IoTReady/low-power-nrf52-weighing-scale/firmware/platform/weighing_scale_hx711.h

/**
 *  pca10040.h : PCA10040 board definitions
 *  Copyright (C) 2019  Appiko
 *
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
 *  You should have received a copy of the GNU General Public License
 *  along with this program.  If not, see <https://www.gnu.org/licenses/>.
 */

/**
 * @addtogroup group_platform
 * @{
 *
 * @defgroup board_pca10040 PCA10040 nRF52-DK
 * @brief The nRF52 Development Kit (DK) platform PCA10040
 * @{
 */

#ifndef PLATFORM_W_SCALE_HX711
#define PLATFORM_W_SCALE_HX711

/** @anchor general-gpio
 * @name General GPIO definitions
 * @{*/
#define GPIO_0          (17)
#define GPIO_1          (16)
#define GPIO_2          (15)
#define GPIO_3          (14)
/** The output level at which the LEDs shine */
#define LEDS_ACTIVE_STATE (0)
/** @} */

/** @anchor weighing_scale_button
 * @name Button Pins
 * @{*/
#define BUTTON_PIN      (7)
/** The input level when the button is pressed */
#define BUTTONS_ACTIVE_STATE (0)
/** The kind of internal resistors required for the button */
#define BUTTON_PULL     (HAL_GPIO_PULLUP)
/** @} */

/** @anchor weighing_scale_serial_interface
 * @name Serial port definitions for Weighing Scale HX711 board
 * @{*/
#define RX_PIN_NUMBER   (21)
#define TX_PIN_NUMBER   (20)
#define CTS_PIN_NUMBER  (7)
#define RTS_PIN_NUMBER  (5)
/** Bool to say if the hardware flow control is required */
#define HWFC            (false)
/** @} */

/** @anchor e_ink_paper_interface 
 * @name E-Ink Paper display Interface
 * @{*/
#define EINK_BUSY       (GPIO_0)
#define EINK_RST        (GPIO_1)
#define EINK_DC         (GPIO_2)
#define EINK_CS         (GPIO_3)
#define EINK_SCLK       (TX_PIN_NUMBER)
#define EINK_MOSI       (RX_PIN_NUMBER)
#define EINK_MISO       (31) //Unused
/** @} */

#if 0
#define EINK_BUSY       (25)
#define EINK_RST        (26)
#define EINK_DC         (27)
#define EINK_CS         (28)
#define EINK_SCLK       (29)
#define EINK_MOSI       (30)
#endif

/** @anchor hx711_interface 
 * @name HX711 Interface
 * @{*/
#define HX711_CLK       (13)
#define HX711_DATA      (12)
#define HX711_RATE      (11)
#define VLC_PIN         (4)
#define LDO_EN          (8)
#define BOOST_EN        (9)
/** @} */

/** @anchor batt_level 
 * @name Battery Level
 * @{*/
#define BT_LV           (5)
#define BT_LV_ANALOG    (ANALOG_PIN_5)
#define BT_LV_EN        (10)
/** @} */

///Bool define if the circuitry is present for the internal DC-DC of nRF52
#define DC_DC_CIRCUITRY     true

///Bool define if a NFC Antenna circuitry is present
#define NFC_CIRCUITRY       true

///Bool define if the 32 kHz crystal is present for the LFCLK
#define LFCLK_XTAL_PRESENT  true

///Bool define if a crystal is present for the HFCLK
#define HFCLK_XTAL_PRESENT  true

/** Low frequency clock source used when initializing the SoftDevice */
#define BOARD_LFCLKSRC_STRUCT  {.source        = NRF_CLOCK_LF_SRC_XTAL,            \
                                    .rc_ctiv       = 0,                                \
                                    .rc_temp_ctiv  = 0,                                \
                                    .accuracy = NRF_CLOCK_LF_ACCURACY_20_PPM}

#define BOARD_LFCLKSRC         LFCLK_SRC_Xtal

#endif /* PLATFORM_W_SCALE_HX711 */

/** @} */
/** @} */
