IoTReady/low-power-nrf52-weighing-scale/firmware/codebase/nrf_core/nrf52810_peripherals.h

/*

Copyright (c) 2010 - 2018, Nordic Semiconductor ASA All rights reserved.

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
1. Redistributions of source code must retain the above copyright notice, this
   list of conditions and the following disclaimer.

2. Redistributions in binary form must reproduce the above copyright
   notice, this list of conditions and the following disclaimer in the
   documentation and/or other materials provided with the distribution.

3. Neither the name of Nordic Semiconductor ASA nor the names of its
   contributors may be used to endorse or promote products derived from this
   software without specific prior written permission.

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
*/

#ifndef _NRF52810_PERIPHERALS_H
#define _NRF52810_PERIPHERALS_H


/* Power Peripheral */
#define POWER_PRESENT
#define POWER_COUNT 1

#define POWER_FEATURE_RAM_REGISTERS_PRESENT
#define POWER_FEATURE_RAM_REGISTERS_COUNT       3

/* Systick timer */
#define SYSTICK_PRESENT
#define SYSTICK_COUNT 1

/* Software Interrupts */
#define SWI_PRESENT
#define SWI_COUNT 6

/* GPIO */
#define GPIO_PRESENT
#define GPIO_COUNT 1

#define P0_PIN_NUM 32

/* MPU and BPROT */
#define BPROT_PRESENT

#define BPROT_REGIONS_SIZE 4096
#define BPROT_REGIONS_NUM 48

/* Radio */
#define RADIO_PRESENT
#define RADIO_COUNT 1

#define RADIO_EASYDMA_MAXCNT_SIZE 8

/* Accelerated Address Resolver */
#define AAR_PRESENT
#define AAR_COUNT 1

#define AAR_MAX_IRK_NUM 16

/* AES Electronic CodeBook mode encryption */
#define ECB_PRESENT
#define ECB_COUNT 1

/* AES CCM mode encryption */
#define CCM_PRESENT
#define CCM_COUNT 1

/* Peripheral to Peripheral Interconnect */
#define PPI_PRESENT
#define PPI_COUNT 1

#define PPI_CH_NUM 20
#define PPI_FIXED_CH_NUM 12
#define PPI_GROUP_NUM 6
#define PPI_FEATURE_FORKS_PRESENT

/* Event Generator Unit */
#define EGU_PRESENT
#define EGU_COUNT 2

#define EGU0_CH_NUM 16
#define EGU1_CH_NUM 16

/* Timer/Counter */
#define TIMER_PRESENT
#define TIMER_COUNT 3

#define TIMER0_MAX_SIZE 32
#define TIMER1_MAX_SIZE 32
#define TIMER2_MAX_SIZE 32

#define TIMER0_CC_NUM 4
#define TIMER1_CC_NUM 4
#define TIMER2_CC_NUM 4

/* Real Time Counter */
#define RTC_PRESENT
#define RTC_COUNT 2

#define RTC0_CC_NUM 3
#define RTC1_CC_NUM 4

/* RNG */
#define RNG_PRESENT
#define RNG_COUNT 1

/* Watchdog Timer */
#define WDT_PRESENT
#define WDT_COUNT 1

/* Temperature Sensor */
#define TEMP_PRESENT
#define TEMP_COUNT 1

/* Serial Peripheral Interface Master with DMA */
#define SPIM_PRESENT
#define SPIM_COUNT 1

#define SPIM0_MAX_DATARATE  8

#define SPIM0_FEATURE_HARDWARE_CSN_PRESENT  0

#define SPIM0_FEATURE_DCX_PRESENT  0

#define SPIM0_FEATURE_RXDELAY_PRESENT  0

#define SPIM0_EASYDMA_MAXCNT_SIZE 10

/* Serial Peripheral Interface Slave with DMA*/
#define SPIS_PRESENT
#define SPIS_COUNT 1

#define SPIS0_EASYDMA_MAXCNT_SIZE 10

/* Two Wire Interface Master with DMA */
#define TWIM_PRESENT
#define TWIM_COUNT 1

#define TWIM0_EASYDMA_MAXCNT_SIZE 10

/* Two Wire Interface Slave with DMA */
#define TWIS_PRESENT
#define TWIS_COUNT 1

#define TWIS0_EASYDMA_MAXCNT_SIZE 10

/* Universal Asynchronous Receiver-Transmitter with DMA */
#define UARTE_PRESENT
#define UARTE_COUNT 1

#define UARTE0_EASYDMA_MAXCNT_SIZE 10

/* Quadrature Decoder */
#define QDEC_PRESENT
#define QDEC_COUNT 1

/* Successive Approximation Analog to Digital Converter */
#define SAADC_PRESENT
#define SAADC_COUNT 1

#define SAADC_EASYDMA_MAXCNT_SIZE 15

#define SAADC_CH_NUM 8

/* GPIO Tasks and Events */
#define GPIOTE_PRESENT
#define GPIOTE_COUNT 1

#define GPIOTE_CH_NUM 8

#define GPIOTE_FEATURE_SET_PRESENT
#define GPIOTE_FEATURE_CLR_PRESENT

/* Comparator */
#define COMP_PRESENT
#define COMP_COUNT 1

/* Pulse Width Modulator */
#define PWM_PRESENT
#define PWM_COUNT 1

#define PWM0_CH_NUM 4

#define PWM0_EASYDMA_MAXCNT_SIZE 15

/* Pulse Density Modulator */
#define PDM_PRESENT
#define PDM_COUNT 1

#define PDM_EASYDMA_MAXCNT_SIZE 15


#endif      // _NRF52810_PERIPHERALS_H
