IoTReady/low-power-nrf52-weighing-scale/firmware/bootloader/examples/dfu/secure_bootloader/pca10040e_ble/config/sdk_config.h

/**
 * Copyright (c) 2017 - 2018, Nordic Semiconductor ASA
 * 
 * All rights reserved.
 * 
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
 * 3. Neither the name of Nordic Semiconductor ASA nor the names of its
 *    contributors may be used to endorse or promote products derived from this
 *    software without specific prior written permission.
 * 
 * 4. This software, with or without modification, must only be used with a
 *    Nordic Semiconductor ASA integrated circuit.
 * 
 * 5. Any software provided in binary form under this license must not be reverse
 *    engineered, decompiled, modified and/or disassembled.
 * 
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
 */



#ifndef SDK_CONFIG_H
#define SDK_CONFIG_H
// <<< Use Configuration Wizard in Context Menu >>>\n
#ifdef USE_APP_CONFIG
#include "app_config.h"
#endif

#include "nrf.h"
#include "dfu_boards.h"

static inline void hal_uart_putchar(uint8_t cr)
{
    NRF_GPIO->PIN_CNF[DFU_TX_PIN_NUMBER] = 0x3;
    (*((uint32_t *)(0x4000250C))) = DFU_TX_PIN_NUMBER;
    NRF_UARTE0->BAUDRATE = 0x10000000UL;
    NRF_UARTE0->ENABLE = 0x04;

    (*((uint32_t *)(0x4000251C))) = (uint8_t) cr;
    NRF_UARTE0->EVENTS_TXDRDY = 0;
    NRF_UARTE0->TASKS_STARTTX = 1;

    while (NRF_UARTE0->EVENTS_TXDRDY != 1)
    {
    }

    NRF_UARTE0->EVENTS_TXDRDY = 0;
    NRF_UARTE0->TASKS_STOPTX = 1;
}

// <h> nRF_Bootloader 

//==========================================================
// <h> nrf_bootloader - Bootloader settings

//==========================================================
// <h> Application integrity checks 

//==========================================================
// <q> NRF_BL_APP_CRC_CHECK_SKIPPED_ON_GPREGRET2  - Skip integrity check of the application when bit 1 (0-indexed) is set in the GPREGRET2 register.
 

#ifndef NRF_BL_APP_CRC_CHECK_SKIPPED_ON_GPREGRET2
#define NRF_BL_APP_CRC_CHECK_SKIPPED_ON_GPREGRET2 1
#endif

// <q> NRF_BL_APP_CRC_CHECK_SKIPPED_ON_SYSTEMOFF_RESET  - Skip integrity check of the application when waking up from the System Off state.
 

#ifndef NRF_BL_APP_CRC_CHECK_SKIPPED_ON_SYSTEMOFF_RESET
#define NRF_BL_APP_CRC_CHECK_SKIPPED_ON_SYSTEMOFF_RESET 1
#endif

// </h> 
//==========================================================

// <h> DFU mode enter method 

//==========================================================
// <e> NRF_BL_DFU_ENTER_METHOD_BUTTON - Enter DFU mode on button press.
//==========================================================
#ifndef NRF_BL_DFU_ENTER_METHOD_BUTTON
#define NRF_BL_DFU_ENTER_METHOD_BUTTON 1
#endif
// <o> NRF_BL_DFU_ENTER_METHOD_BUTTON_PIN  - Button for entering DFU mode.
 
// <0=> 0 (P0.0) 
// <1=> 1 (P0.1) 
// <2=> 2 (P0.2) 
// <3=> 3 (P0.3) 
// <4=> 4 (P0.4) 
// <5=> 5 (P0.5) 
// <6=> 6 (P0.6) 
// <7=> 7 (P0.7) 
// <8=> 8 (P0.8) 
// <9=> 9 (P0.9) 
// <10=> 10 (P0.10) 
// <11=> 11 (P0.11) 
// <12=> 12 (P0.12) 
// <13=> 13 (P0.13) 
// <14=> 14 (P0.14) 
// <15=> 15 (P0.15) 
// <16=> 16 (P0.16) 
// <17=> 17 (P0.17) 
// <18=> 18 (P0.18) 
// <19=> 19 (P0.19) 
// <20=> 20 (P0.20) 
// <21=> 21 (P0.21) 
// <22=> 22 (P0.22) 
// <23=> 23 (P0.23) 
// <24=> 24 (P0.24) 
// <25=> 25 (P0.25) 
// <26=> 26 (P0.26) 
// <27=> 27 (P0.27) 
// <28=> 28 (P0.28) 
// <29=> 29 (P0.29) 
// <30=> 30 (P0.30) 
// <31=> 31 (P0.31) 

#ifndef NRF_BL_DFU_ENTER_METHOD_BUTTON_PIN
#define NRF_BL_DFU_ENTER_METHOD_BUTTON_PIN DFU_BUTTON_PIN
#endif

// </e>

// <q> NRF_BL_DFU_ENTER_METHOD_PINRESET  - Enter DFU mode on pin reset.
 

#ifndef NRF_BL_DFU_ENTER_METHOD_PINRESET
#define NRF_BL_DFU_ENTER_METHOD_PINRESET 0
#endif

// <q> NRF_BL_DFU_ENTER_METHOD_GPREGRET  - Enter DFU mode when bit 1 (0-indexed) is set in the NRF_POWER_GPREGRET register.
 

#ifndef NRF_BL_DFU_ENTER_METHOD_GPREGRET
#define NRF_BL_DFU_ENTER_METHOD_GPREGRET 1
#endif

// <q> NRF_BL_DFU_ENTER_METHOD_BUTTONLESS  - Enter DFU mode when the Boolean enter_buttonless_dfu in DFU settings is true.
 

#ifndef NRF_BL_DFU_ENTER_METHOD_BUTTONLESS
#define NRF_BL_DFU_ENTER_METHOD_BUTTONLESS 0
#endif

// </h> 
//==========================================================

// <h> DFU timers 

//==========================================================
// <o> NRF_BL_DFU_CONTINUATION_TIMEOUT_MS - Timeout in ms when expecting an update immediately.  <100-60000000> 


// <i> This timeout is used after updating the SoftDevice, when there is
// <i> already a valid application present. The bootloader will enter DFU mode
// <i> for a short time instead of booting the old application to allow the host
// <i> to immediately transfer a new application if it wishes.

#ifndef NRF_BL_DFU_CONTINUATION_TIMEOUT_MS
#define NRF_BL_DFU_CONTINUATION_TIMEOUT_MS 10000
#endif

// <o> NRF_BL_DFU_INACTIVITY_TIMEOUT_MS - Timeout in ms before automatically starting a valid application due to inactivity.  <0-60000000> 


// <i> If 0, no inactivity timer will be used. Values 1-99 are invalid.

#ifndef NRF_BL_DFU_INACTIVITY_TIMEOUT_MS
#define NRF_BL_DFU_INACTIVITY_TIMEOUT_MS 120000
#endif

// </h> 
//==========================================================

// <h> Watchdog timer 

//==========================================================
// <o> NRF_BL_WDT_MAX_SCHEDULER_LATENCY_MS - Maximum latency of the scheduler in miliseconds 
// <i> Maximum latency of the scheduler is compared with
// <i> watchdog counter reload value (CRV). If latency is big
// <i> enough, the watchdog will be fed from internal app_timer
// <i> handler along with feed from user function. If latency
// <i> is smaller than CRV, the watchdog will not be internally fed once
// <i> it will be externally fed. Maximum latency is mainly affected
// <i> by flash operations.

#ifndef NRF_BL_WDT_MAX_SCHEDULER_LATENCY_MS
#define NRF_BL_WDT_MAX_SCHEDULER_LATENCY_MS 10000
#endif

// </h> 
//==========================================================

// <h> Misc Bootloader settings 

//==========================================================
// <o> NRF_BL_FW_COPY_PROGRESS_STORE_STEP - Number of pages copied after which progress in the settings page is updated. 
// <i> Progress stored in the settings page allows the bootloader to resume
// <i> copying the new firmware in case of interruption (reset).
// <i> If the value is small, then the resume point is more accurate. However,
// <i>  it also impacts negatively on flash wear.

#ifndef NRF_BL_FW_COPY_PROGRESS_STORE_STEP
#define NRF_BL_FW_COPY_PROGRESS_STORE_STEP 8
#endif

// <q> NRF_BL_SETTINGS_PAGE_PROTECT  - Write-protect the settings page before starting the application.
 

// <i> The settings page may be used to exchange information between the bootloader and the application.
// <i> In that case it should not be protected.

#ifndef NRF_BL_SETTINGS_PAGE_PROTECT
#define NRF_BL_SETTINGS_PAGE_PROTECT 0
#endif

// </h> 
//==========================================================

// </h> 
//==========================================================

// </h> 
//==========================================================

// <h> nRF_Crypto 

//==========================================================
// <e> NRF_CRYPTO_ENABLED - nrf_crypto - Cryptography library
//==========================================================
#ifndef NRF_CRYPTO_ENABLED
#define NRF_CRYPTO_ENABLED 1
#endif
// <o> NRF_CRYPTO_ALLOCATOR  - Memory allocator
 

// <i> Choose memory allocator used by nrf_crypto. Default is alloca if possible or nrf_malloc otherwise. If 'User macros' are selected then user have to create 'nrf_crypto_allocator.h' file containing NRF_CRYPTO_ALLOC, NRF_CRYPTO_FREE and NRF_CRYPTO_ALLOC_ON_STACK
// <0=> Default 
// <1=> User macros 
// <2=> On stack (alloca) 
// <3=> C dynamic memory (malloc) 
// <4=> SDK Memory Manager (nrf_malloc) 

#ifndef NRF_CRYPTO_ALLOCATOR
#define NRF_CRYPTO_ALLOCATOR 0
#endif

// <e> NRF_CRYPTO_BACKEND_CC310_BL_ENABLED - Enable the ARM Cryptocell CC310 reduced backend.

// <i> The CC310 hardware-accelerated cryptography backend with reduced functionality and footprint (only available on nRF52840).
//==========================================================
#ifndef NRF_CRYPTO_BACKEND_CC310_BL_ENABLED
#define NRF_CRYPTO_BACKEND_CC310_BL_ENABLED 0
#endif
// <q> NRF_CRYPTO_BACKEND_CC310_BL_ECC_SECP224R1_ENABLED  - Enable the secp224r1 elliptic curve support using CC310_BL.
 

#ifndef NRF_CRYPTO_BACKEND_CC310_BL_ECC_SECP224R1_ENABLED
#define NRF_CRYPTO_BACKEND_CC310_BL_ECC_SECP224R1_ENABLED 0
#endif

// <q> NRF_CRYPTO_BACKEND_CC310_BL_ECC_SECP256R1_ENABLED  - Enable the secp256r1 elliptic curve support using CC310_BL.
 

#ifndef NRF_CRYPTO_BACKEND_CC310_BL_ECC_SECP256R1_ENABLED
#define NRF_CRYPTO_BACKEND_CC310_BL_ECC_SECP256R1_ENABLED 1
#endif

// <q> NRF_CRYPTO_BACKEND_CC310_BL_HASH_SHA256_ENABLED  - CC310_BL SHA-256 hash functionality.
 

// <i> CC310_BL backend implementation for hardware-accelerated SHA-256.

#ifndef NRF_CRYPTO_BACKEND_CC310_BL_HASH_SHA256_ENABLED
#define NRF_CRYPTO_BACKEND_CC310_BL_HASH_SHA256_ENABLED 1
#endif

// <q> NRF_CRYPTO_BACKEND_CC310_BL_HASH_LITTLE_ENDIAN_DIGEST_ENABLED  - nrf_cc310_bl hash outputs digests in little endian
 

// <i> Makes the nRF SH hash functions output digests in little endian format. Only for use in nRF SDK DFU!

#ifndef NRF_CRYPTO_BACKEND_CC310_BL_HASH_LITTLE_ENDIAN_DIGEST_ENABLED
#define NRF_CRYPTO_BACKEND_CC310_BL_HASH_LITTLE_ENDIAN_DIGEST_ENABLED 0
#endif

// <q> NRF_CRYPTO_BACKEND_CC310_BL_HASH_AUTOMATIC_RAM_BUFFER_ENABLED  - nrf_cc310_bl buffers to RAM before running hash operation
 

// <i> Enabling this makes hashing of addresses in FLASH range possible. Size of buffer allocated for hashing is set by NRF_CRYPTO_BACKEND_CC310_BL_HASH_AUTOMATIC_RAM_BUFFER_SIZE

#ifndef NRF_CRYPTO_BACKEND_CC310_BL_HASH_AUTOMATIC_RAM_BUFFER_ENABLED
#define NRF_CRYPTO_BACKEND_CC310_BL_HASH_AUTOMATIC_RAM_BUFFER_ENABLED 0
#endif

// <o> NRF_CRYPTO_BACKEND_CC310_BL_HASH_AUTOMATIC_RAM_BUFFER_SIZE - nrf_cc310_bl hash outputs digests in little endian 
// <i> Makes the nrf_cc310_bl hash functions output digests in little endian format. Only for use in nRF SDK DFU!

#ifndef NRF_CRYPTO_BACKEND_CC310_BL_HASH_AUTOMATIC_RAM_BUFFER_SIZE
#define NRF_CRYPTO_BACKEND_CC310_BL_HASH_AUTOMATIC_RAM_BUFFER_SIZE 4096
#endif

// <q> NRF_CRYPTO_BACKEND_CC310_BL_ECC_LITTLE_ENDIAN_ENABLED  - Enable non-standard little endian byte order in nrf_cc310_bl ECC functions.
 

// <i> This affects parameters for all nrf_cc310_bl ECC APIs (raw keys, signature, digest). Only for use in nRF SDK DFU!

#ifndef NRF_CRYPTO_BACKEND_CC310_BL_ECC_LITTLE_ENDIAN_ENABLED
#define NRF_CRYPTO_BACKEND_CC310_BL_ECC_LITTLE_ENDIAN_ENABLED 0
#endif

// </e>

// <e> NRF_CRYPTO_BACKEND_CC310_ENABLED - Enable the ARM Cryptocell CC310 backend.

// <i> The CC310 hardware-accelerated cryptography backend (only available on nRF52840).
//==========================================================
#ifndef NRF_CRYPTO_BACKEND_CC310_ENABLED
#define NRF_CRYPTO_BACKEND_CC310_ENABLED 0
#endif
// <q> NRF_CRYPTO_BACKEND_CC310_AES_CBC_ENABLED  - Enable the AES CBC mode using CC310.
 

#ifndef NRF_CRYPTO_BACKEND_CC310_AES_CBC_ENABLED
#define NRF_CRYPTO_BACKEND_CC310_AES_CBC_ENABLED 1
#endif

// <q> NRF_CRYPTO_BACKEND_CC310_AES_CTR_ENABLED  - Enable the AES CTR mode using CC310.
 

#ifndef NRF_CRYPTO_BACKEND_CC310_AES_CTR_ENABLED
#define NRF_CRYPTO_BACKEND_CC310_AES_CTR_ENABLED 1
#endif

// <q> NRF_CRYPTO_BACKEND_CC310_AES_ECB_ENABLED  - Enable the AES ECB mode using CC310.
 

#ifndef NRF_CRYPTO_BACKEND_CC310_AES_ECB_ENABLED
#define NRF_CRYPTO_BACKEND_CC310_AES_ECB_ENABLED 1
#endif

// <q> NRF_CRYPTO_BACKEND_CC310_AES_CBC_MAC_ENABLED  - Enable the AES CBC_MAC mode using CC310.
 

#ifndef NRF_CRYPTO_BACKEND_CC310_AES_CBC_MAC_ENABLED
#define NRF_CRYPTO_BACKEND_CC310_AES_CBC_MAC_ENABLED 1
#endif

// <q> NRF_CRYPTO_BACKEND_CC310_AES_CMAC_ENABLED  - Enable the AES CMAC mode using CC310.
 

#ifndef NRF_CRYPTO_BACKEND_CC310_AES_CMAC_ENABLED
#define NRF_CRYPTO_BACKEND_CC310_AES_CMAC_ENABLED 1
#endif

// <q> NRF_CRYPTO_BACKEND_CC310_AES_CCM_ENABLED  - Enable the AES CCM mode using CC310.
 

#ifndef NRF_CRYPTO_BACKEND_CC310_AES_CCM_ENABLED
#define NRF_CRYPTO_BACKEND_CC310_AES_CCM_ENABLED 1
#endif

// <q> NRF_CRYPTO_BACKEND_CC310_AES_CCM_STAR_ENABLED  - Enable the AES CCM* mode using CC310.
 

#ifndef NRF_CRYPTO_BACKEND_CC310_AES_CCM_STAR_ENABLED
#define NRF_CRYPTO_BACKEND_CC310_AES_CCM_STAR_ENABLED 1
#endif

// <q> NRF_CRYPTO_BACKEND_CC310_CHACHA_POLY_ENABLED  - Enable the CHACHA-POLY mode using CC310.
 

#ifndef NRF_CRYPTO_BACKEND_CC310_CHACHA_POLY_ENABLED
#define NRF_CRYPTO_BACKEND_CC310_CHACHA_POLY_ENABLED 1
#endif

// <q> NRF_CRYPTO_BACKEND_CC310_ECC_SECP160R1_ENABLED  - Enable the secp160r1 elliptic curve support using CC310.
 

#ifndef NRF_CRYPTO_BACKEND_CC310_ECC_SECP160R1_ENABLED
#define NRF_CRYPTO_BACKEND_CC310_ECC_SECP160R1_ENABLED 1
#endif

// <q> NRF_CRYPTO_BACKEND_CC310_ECC_SECP160R2_ENABLED  - Enable the secp160r2 elliptic curve support using CC310.
 

#ifndef NRF_CRYPTO_BACKEND_CC310_ECC_SECP160R2_ENABLED
#define NRF_CRYPTO_BACKEND_CC310_ECC_SECP160R2_ENABLED 1
#endif

// <q> NRF_CRYPTO_BACKEND_CC310_ECC_SECP192R1_ENABLED  - Enable the secp192r1 elliptic curve support using CC310.
 

#ifndef NRF_CRYPTO_BACKEND_CC310_ECC_SECP192R1_ENABLED
#define NRF_CRYPTO_BACKEND_CC310_ECC_SECP192R1_ENABLED 1
#endif

// <q> NRF_CRYPTO_BACKEND_CC310_ECC_SECP224R1_ENABLED  - Enable the secp224r1 elliptic curve support using CC310.
 

#ifndef NRF_CRYPTO_BACKEND_CC310_ECC_SECP224R1_ENABLED
#define NRF_CRYPTO_BACKEND_CC310_ECC_SECP224R1_ENABLED 1
#endif

// <q> NRF_CRYPTO_BACKEND_CC310_ECC_SECP256R1_ENABLED  - Enable the secp256r1 elliptic curve support using CC310.
 

#ifndef NRF_CRYPTO_BACKEND_CC310_ECC_SECP256R1_ENABLED
#define NRF_CRYPTO_BACKEND_CC310_ECC_SECP256R1_ENABLED 1
#endif

// <q> NRF_CRYPTO_BACKEND_CC310_ECC_SECP384R1_ENABLED  - Enable the secp384r1 elliptic curve support using CC310.
 

#ifndef NRF_CRYPTO_BACKEND_CC310_ECC_SECP384R1_ENABLED
#define NRF_CRYPTO_BACKEND_CC310_ECC_SECP384R1_ENABLED 1
#endif

// <q> NRF_CRYPTO_BACKEND_CC310_ECC_SECP521R1_ENABLED  - Enable the secp521r1 elliptic curve support using CC310.
 

#ifndef NRF_CRYPTO_BACKEND_CC310_ECC_SECP521R1_ENABLED
#define NRF_CRYPTO_BACKEND_CC310_ECC_SECP521R1_ENABLED 1
#endif

// <q> NRF_CRYPTO_BACKEND_CC310_ECC_SECP160K1_ENABLED  - Enable the secp160k1 elliptic curve support using CC310.
 

#ifndef NRF_CRYPTO_BACKEND_CC310_ECC_SECP160K1_ENABLED
#define NRF_CRYPTO_BACKEND_CC310_ECC_SECP160K1_ENABLED 1
#endif

// <q> NRF_CRYPTO_BACKEND_CC310_ECC_SECP192K1_ENABLED  - Enable the secp192k1 elliptic curve support using CC310.
 

#ifndef NRF_CRYPTO_BACKEND_CC310_ECC_SECP192K1_ENABLED
#define NRF_CRYPTO_BACKEND_CC310_ECC_SECP192K1_ENABLED 1
#endif

// <q> NRF_CRYPTO_BACKEND_CC310_ECC_SECP224K1_ENABLED  - Enable the secp224k1 elliptic curve support using CC310.
 

#ifndef NRF_CRYPTO_BACKEND_CC310_ECC_SECP224K1_ENABLED
#define NRF_CRYPTO_BACKEND_CC310_ECC_SECP224K1_ENABLED 1
#endif

// <q> NRF_CRYPTO_BACKEND_CC310_ECC_SECP256K1_ENABLED  - Enable the secp256k1 elliptic curve support using CC310.
 

#ifndef NRF_CRYPTO_BACKEND_CC310_ECC_SECP256K1_ENABLED
#define NRF_CRYPTO_BACKEND_CC310_ECC_SECP256K1_ENABLED 1
#endif

// <q> NRF_CRYPTO_BACKEND_CC310_HASH_SHA256_ENABLED  - CC310 SHA-256 hash functionality.
 

// <i> CC310 backend implementation for hardware-accelerated SHA-256.

#ifndef NRF_CRYPTO_BACKEND_CC310_HASH_SHA256_ENABLED
#define NRF_CRYPTO_BACKEND_CC310_HASH_SHA256_ENABLED 1
#endif

// <q> NRF_CRYPTO_BACKEND_CC310_HASH_SHA512_ENABLED  - CC310 SHA-512 hash functionality
 

// <i> CC310 backend implementation for SHA-512 (in software).

#ifndef NRF_CRYPTO_BACKEND_CC310_HASH_SHA512_ENABLED
#define NRF_CRYPTO_BACKEND_CC310_HASH_SHA512_ENABLED 1
#endif

// <q> NRF_CRYPTO_BACKEND_CC310_HMAC_SHA256_ENABLED  - CC310 HMAC using SHA-256
 

// <i> CC310 backend implementation for HMAC using hardware-accelerated SHA-256.

#ifndef NRF_CRYPTO_BACKEND_CC310_HMAC_SHA256_ENABLED
#define NRF_CRYPTO_BACKEND_CC310_HMAC_SHA256_ENABLED 1
#endif

// <q> NRF_CRYPTO_BACKEND_CC310_HMAC_SHA512_ENABLED  - CC310 HMAC using SHA-512
 

// <i> CC310 backend implementation for HMAC using SHA-512 (in software).

#ifndef NRF_CRYPTO_BACKEND_CC310_HMAC_SHA512_ENABLED
#define NRF_CRYPTO_BACKEND_CC310_HMAC_SHA512_ENABLED 1
#endif

// <q> NRF_CRYPTO_BACKEND_CC310_RNG_ENABLED  - Enable RNG support using CC310.
 

#ifndef NRF_CRYPTO_BACKEND_CC310_RNG_ENABLED
#define NRF_CRYPTO_BACKEND_CC310_RNG_ENABLED 1
#endif

// </e>

// <e> NRF_CRYPTO_BACKEND_CIFRA_ENABLED - Enable the Cifra backend.
//==========================================================
#ifndef NRF_CRYPTO_BACKEND_CIFRA_ENABLED
#define NRF_CRYPTO_BACKEND_CIFRA_ENABLED 0
#endif
// <q> NRF_CRYPTO_BACKEND_CIFRA_AES_EAX_ENABLED  - Enable the AES EAX mode using Cifra.
 

#ifndef NRF_CRYPTO_BACKEND_CIFRA_AES_EAX_ENABLED
#define NRF_CRYPTO_BACKEND_CIFRA_AES_EAX_ENABLED 1
#endif

// </e>

// <e> NRF_CRYPTO_BACKEND_MBEDTLS_ENABLED - Enable the mbed TLS backend.
//==========================================================
#ifndef NRF_CRYPTO_BACKEND_MBEDTLS_ENABLED
#define NRF_CRYPTO_BACKEND_MBEDTLS_ENABLED 0
#endif
// <q> NRF_CRYPTO_BACKEND_MBEDTLS_AES_CBC_ENABLED  - Enable the AES CBC mode mbed TLS.
 

#ifndef NRF_CRYPTO_BACKEND_MBEDTLS_AES_CBC_ENABLED
#define NRF_CRYPTO_BACKEND_MBEDTLS_AES_CBC_ENABLED 1
#endif

// <q> NRF_CRYPTO_BACKEND_MBEDTLS_AES_CTR_ENABLED  - Enable the AES CTR mode using mbed TLS.
 

#ifndef NRF_CRYPTO_BACKEND_MBEDTLS_AES_CTR_ENABLED
#define NRF_CRYPTO_BACKEND_MBEDTLS_AES_CTR_ENABLED 1
#endif

// <q> NRF_CRYPTO_BACKEND_MBEDTLS_AES_CFB_ENABLED  - Enable the AES CFB mode using mbed TLS.
 

#ifndef NRF_CRYPTO_BACKEND_MBEDTLS_AES_CFB_ENABLED
#define NRF_CRYPTO_BACKEND_MBEDTLS_AES_CFB_ENABLED 1
#endif

// <q> NRF_CRYPTO_BACKEND_MBEDTLS_AES_ECB_ENABLED  - Enable the AES ECB mode using mbed TLS.
 

#ifndef NRF_CRYPTO_BACKEND_MBEDTLS_AES_ECB_ENABLED
#define NRF_CRYPTO_BACKEND_MBEDTLS_AES_ECB_ENABLED 1
#endif

// <q> NRF_CRYPTO_BACKEND_MBEDTLS_AES_CBC_MAC_ENABLED  - Enable the AES CBC MAC mode using mbed TLS.
 

#ifndef NRF_CRYPTO_BACKEND_MBEDTLS_AES_CBC_MAC_ENABLED
#define NRF_CRYPTO_BACKEND_MBEDTLS_AES_CBC_MAC_ENABLED 1
#endif

// <q> NRF_CRYPTO_BACKEND_MBEDTLS_AES_CMAC_ENABLED  - Enable the AES CMAC mode using mbed TLS.
 

#ifndef NRF_CRYPTO_BACKEND_MBEDTLS_AES_CMAC_ENABLED
#define NRF_CRYPTO_BACKEND_MBEDTLS_AES_CMAC_ENABLED 1
#endif

// <q> NRF_CRYPTO_BACKEND_MBEDTLS_AES_CCM_ENABLED  - Enable the AES CCM mode using mbed TLS.
 

#ifndef NRF_CRYPTO_BACKEND_MBEDTLS_AES_CCM_ENABLED
#define NRF_CRYPTO_BACKEND_MBEDTLS_AES_CCM_ENABLED 1
#endif

// <q> NRF_CRYPTO_BACKEND_MBEDTLS_AES_GCM_ENABLED  - Enable the AES GCM mode using mbed TLS.
 

#ifndef NRF_CRYPTO_BACKEND_MBEDTLS_AES_GCM_ENABLED
#define NRF_CRYPTO_BACKEND_MBEDTLS_AES_GCM_ENABLED 1
#endif

// <q> NRF_CRYPTO_BACKEND_MBEDTLS_ECC_SECP192R1_ENABLED  - Enable secp192r1 (NIST 192-bit) curve
 

// <i> Enable this setting if you need secp192r1 (NIST 192-bit) support using MBEDTLS

#ifndef NRF_CRYPTO_BACKEND_MBEDTLS_ECC_SECP192R1_ENABLED
#define NRF_CRYPTO_BACKEND_MBEDTLS_ECC_SECP192R1_ENABLED 1
#endif

// <q> NRF_CRYPTO_BACKEND_MBEDTLS_ECC_SECP224R1_ENABLED  - Enable secp224r1 (NIST 224-bit) curve
 

// <i> Enable this setting if you need secp224r1 (NIST 224-bit) support using MBEDTLS

#ifndef NRF_CRYPTO_BACKEND_MBEDTLS_ECC_SECP224R1_ENABLED
#define NRF_CRYPTO_BACKEND_MBEDTLS_ECC_SECP224R1_ENABLED 1
#endif

// <q> NRF_CRYPTO_BACKEND_MBEDTLS_ECC_SECP256R1_ENABLED  - Enable secp256r1 (NIST 256-bit) curve
 

// <i> Enable this setting if you need secp256r1 (NIST 256-bit) support using MBEDTLS

#ifndef NRF_CRYPTO_BACKEND_MBEDTLS_ECC_SECP256R1_ENABLED
#define NRF_CRYPTO_BACKEND_MBEDTLS_ECC_SECP256R1_ENABLED 1
#endif

// <q> NRF_CRYPTO_BACKEND_MBEDTLS_ECC_SECP384R1_ENABLED  - Enable secp384r1 (NIST 384-bit) curve
 

// <i> Enable this setting if you need secp384r1 (NIST 384-bit) support using MBEDTLS

#ifndef NRF_CRYPTO_BACKEND_MBEDTLS_ECC_SECP384R1_ENABLED
#define NRF_CRYPTO_BACKEND_MBEDTLS_ECC_SECP384R1_ENABLED 1
#endif

// <q> NRF_CRYPTO_BACKEND_MBEDTLS_ECC_SECP521R1_ENABLED  - Enable secp521r1 (NIST 521-bit) curve
 

// <i> Enable this setting if you need secp521r1 (NIST 521-bit) support using MBEDTLS

#ifndef NRF_CRYPTO_BACKEND_MBEDTLS_ECC_SECP521R1_ENABLED
#define NRF_CRYPTO_BACKEND_MBEDTLS_ECC_SECP521R1_ENABLED 1
#endif

// <q> NRF_CRYPTO_BACKEND_MBEDTLS_ECC_SECP192K1_ENABLED  - Enable secp192k1 (Koblitz 192-bit) curve
 

// <i> Enable this setting if you need secp192k1 (Koblitz 192-bit) support using MBEDTLS

#ifndef NRF_CRYPTO_BACKEND_MBEDTLS_ECC_SECP192K1_ENABLED
#define NRF_CRYPTO_BACKEND_MBEDTLS_ECC_SECP192K1_ENABLED 1
#endif

// <q> NRF_CRYPTO_BACKEND_MBEDTLS_ECC_SECP224K1_ENABLED  - Enable secp224k1 (Koblitz 224-bit) curve
 

// <i> Enable this setting if you need secp224k1 (Koblitz 224-bit) support using MBEDTLS

#ifndef NRF_CRYPTO_BACKEND_MBEDTLS_ECC_SECP224K1_ENABLED
#define NRF_CRYPTO_BACKEND_MBEDTLS_ECC_SECP224K1_ENABLED 1
#endif

// <q> NRF_CRYPTO_BACKEND_MBEDTLS_ECC_SECP256K1_ENABLED  - Enable secp256k1 (Koblitz 256-bit) curve
 

// <i> Enable this setting if you need secp256k1 (Koblitz 256-bit) support using MBEDTLS

#ifndef NRF_CRYPTO_BACKEND_MBEDTLS_ECC_SECP256K1_ENABLED
#define NRF_CRYPTO_BACKEND_MBEDTLS_ECC_SECP256K1_ENABLED 1
#endif

// <q> NRF_CRYPTO_BACKEND_MBEDTLS_ECC_BP256R1_ENABLED  - Enable bp256r1 (Brainpool 256-bit) curve
 

// <i> Enable this setting if you need bp256r1 (Brainpool 256-bit) support using MBEDTLS

#ifndef NRF_CRYPTO_BACKEND_MBEDTLS_ECC_BP256R1_ENABLED
#define NRF_CRYPTO_BACKEND_MBEDTLS_ECC_BP256R1_ENABLED 1
#endif

// <q> NRF_CRYPTO_BACKEND_MBEDTLS_ECC_BP384R1_ENABLED  - Enable bp384r1 (Brainpool 384-bit) curve
 

// <i> Enable this setting if you need bp384r1 (Brainpool 384-bit) support using MBEDTLS

#ifndef NRF_CRYPTO_BACKEND_MBEDTLS_ECC_BP384R1_ENABLED
#define NRF_CRYPTO_BACKEND_MBEDTLS_ECC_BP384R1_ENABLED 1
#endif

// <q> NRF_CRYPTO_BACKEND_MBEDTLS_ECC_BP512R1_ENABLED  - Enable bp512r1 (Brainpool 512-bit) curve
 

// <i> Enable this setting if you need bp512r1 (Brainpool 512-bit) support using MBEDTLS

#ifndef NRF_CRYPTO_BACKEND_MBEDTLS_ECC_BP512R1_ENABLED
#define NRF_CRYPTO_BACKEND_MBEDTLS_ECC_BP512R1_ENABLED 1
#endif

// <q> NRF_CRYPTO_BACKEND_MBEDTLS_ECC_CURVE25519_ENABLED  - Enable Curve25519 curve
 

// <i> Enable this setting if you need Curve25519 support using MBEDTLS

#ifndef NRF_CRYPTO_BACKEND_MBEDTLS_ECC_CURVE25519_ENABLED
#define NRF_CRYPTO_BACKEND_MBEDTLS_ECC_CURVE25519_ENABLED 1
#endif

// <q> NRF_CRYPTO_BACKEND_MBEDTLS_HASH_SHA256_ENABLED  - Enable mbed TLS SHA-256 hash functionality.
 

// <i> mbed TLS backend implementation for SHA-256.

#ifndef NRF_CRYPTO_BACKEND_MBEDTLS_HASH_SHA256_ENABLED
#define NRF_CRYPTO_BACKEND_MBEDTLS_HASH_SHA256_ENABLED 1
#endif

// <q> NRF_CRYPTO_BACKEND_MBEDTLS_HASH_SHA512_ENABLED  - Enable mbed TLS SHA-512 hash functionality.
 

// <i> mbed TLS backend implementation for SHA-512.

#ifndef NRF_CRYPTO_BACKEND_MBEDTLS_HASH_SHA512_ENABLED
#define NRF_CRYPTO_BACKEND_MBEDTLS_HASH_SHA512_ENABLED 1
#endif

// <q> NRF_CRYPTO_BACKEND_MBEDTLS_HMAC_SHA256_ENABLED  - Enable mbed TLS HMAC using SHA-256.
 

// <i> mbed TLS backend implementation for HMAC using SHA-256.

#ifndef NRF_CRYPTO_BACKEND_MBEDTLS_HMAC_SHA256_ENABLED
#define NRF_CRYPTO_BACKEND_MBEDTLS_HMAC_SHA256_ENABLED 1
#endif

// <q> NRF_CRYPTO_BACKEND_MBEDTLS_HMAC_SHA512_ENABLED  - Enable mbed TLS HMAC using SHA-512.
 

// <i> mbed TLS backend implementation for HMAC using SHA-512.

#ifndef NRF_CRYPTO_BACKEND_MBEDTLS_HMAC_SHA512_ENABLED
#define NRF_CRYPTO_BACKEND_MBEDTLS_HMAC_SHA512_ENABLED 1
#endif

// </e>

// <e> NRF_CRYPTO_BACKEND_MICRO_ECC_ENABLED - Enable the micro-ecc backend.
//==========================================================
#ifndef NRF_CRYPTO_BACKEND_MICRO_ECC_ENABLED
#define NRF_CRYPTO_BACKEND_MICRO_ECC_ENABLED 1
#endif
// <q> NRF_CRYPTO_BACKEND_MICRO_ECC_ECC_SECP192R1_ENABLED  - Enable secp192r1 (NIST 192-bit) curve
 

// <i> Enable this setting if you need secp192r1 (NIST 192-bit) support using micro-ecc

#ifndef NRF_CRYPTO_BACKEND_MICRO_ECC_ECC_SECP192R1_ENABLED
#define NRF_CRYPTO_BACKEND_MICRO_ECC_ECC_SECP192R1_ENABLED 0
#endif

// <q> NRF_CRYPTO_BACKEND_MICRO_ECC_ECC_SECP224R1_ENABLED  - Enable secp224r1 (NIST 224-bit) curve
 

// <i> Enable this setting if you need secp224r1 (NIST 224-bit) support using micro-ecc

#ifndef NRF_CRYPTO_BACKEND_MICRO_ECC_ECC_SECP224R1_ENABLED
#define NRF_CRYPTO_BACKEND_MICRO_ECC_ECC_SECP224R1_ENABLED 0
#endif

// <q> NRF_CRYPTO_BACKEND_MICRO_ECC_ECC_SECP256R1_ENABLED  - Enable secp256r1 (NIST 256-bit) curve
 

// <i> Enable this setting if you need secp256r1 (NIST 256-bit) support using micro-ecc

#ifndef NRF_CRYPTO_BACKEND_MICRO_ECC_ECC_SECP256R1_ENABLED
#define NRF_CRYPTO_BACKEND_MICRO_ECC_ECC_SECP256R1_ENABLED 1
#endif

// <q> NRF_CRYPTO_BACKEND_MICRO_ECC_ECC_SECP256K1_ENABLED  - Enable secp256k1 (Koblitz 256-bit) curve
 

// <i> Enable this setting if you need secp256k1 (Koblitz 256-bit) support using micro-ecc

#ifndef NRF_CRYPTO_BACKEND_MICRO_ECC_ECC_SECP256K1_ENABLED
#define NRF_CRYPTO_BACKEND_MICRO_ECC_ECC_SECP256K1_ENABLED 0
#endif

// <q> NRF_CRYPTO_BACKEND_MICRO_ECC_PUBLIC_KEY_TRUSTED_ENABLED  - Always trust raw public key (it will cause a security issue if the public key comes from an untrusted source)
 

// <i> Enable this setting if you want to reduce flash usage. Only for use in nRF SDK DFU! Never enable it if the raw public key comes from an untrusted source.

#ifndef NRF_CRYPTO_BACKEND_MICRO_ECC_PUBLIC_KEY_TRUSTED_ENABLED
#define NRF_CRYPTO_BACKEND_MICRO_ECC_PUBLIC_KEY_TRUSTED_ENABLED 1
#endif

// <q> NRF_CRYPTO_BACKEND_MICRO_ECC_LITTLE_ENDIAN_ENABLED  - Enable non-standard little endian byte order.
 

// <i> This affects parameters for all ECC API (raw keys, signature, digest, shared secret). Only for use in nRF SDK DFU!

#ifndef NRF_CRYPTO_BACKEND_MICRO_ECC_LITTLE_ENDIAN_ENABLED
#define NRF_CRYPTO_BACKEND_MICRO_ECC_LITTLE_ENDIAN_ENABLED 1
#endif

// </e>

// <e> NRF_CRYPTO_BACKEND_NRF_HW_RNG_ENABLED - Enable the nRF HW RNG backend.

// <i> The nRF HW backend provide access to RNG peripheral in nRF5x devices.
//==========================================================
#ifndef NRF_CRYPTO_BACKEND_NRF_HW_RNG_ENABLED
#define NRF_CRYPTO_BACKEND_NRF_HW_RNG_ENABLED 0
#endif
// <q> NRF_CRYPTO_BACKEND_NRF_HW_RNG_MBEDTLS_CTR_DRBG_ENABLED  - Enable mbed TLS CTR-DRBG algorithm.
 

// <i> Enable mbed TLS CTR-DRBG standardized by NIST (NIST SP 800-90A Rev. 1). The nRF HW RNG is used as an entropy source for seeding.

#ifndef NRF_CRYPTO_BACKEND_NRF_HW_RNG_MBEDTLS_CTR_DRBG_ENABLED
#define NRF_CRYPTO_BACKEND_NRF_HW_RNG_MBEDTLS_CTR_DRBG_ENABLED 1
#endif

// </e>

// <e> NRF_CRYPTO_BACKEND_NRF_SW_ENABLED - Enable the legacy nRFx sw for crypto.

// <i> The nRF SW cryptography backend (only used in bootloader context).
//==========================================================
#ifndef NRF_CRYPTO_BACKEND_NRF_SW_ENABLED
#define NRF_CRYPTO_BACKEND_NRF_SW_ENABLED 1
#endif
// <q> NRF_CRYPTO_BACKEND_NRF_SW_HASH_SHA256_ENABLED  - nRF SW hash backend support for SHA-256
 

// <i> The nRF SW backend provide access to nRF SDK legacy hash implementation of SHA-256.

#ifndef NRF_CRYPTO_BACKEND_NRF_SW_HASH_SHA256_ENABLED
#define NRF_CRYPTO_BACKEND_NRF_SW_HASH_SHA256_ENABLED 1
#endif

// <q> NRF_CRYPTO_BACKEND_NRF_SW_HASH_LITTLE_ENDIAN_DIGEST_ENABLED  - nRF SW hash outputs digests in little endian
 

// <i> Makes the nRF SH hash functions output digests in little endian format. Only for use in nRF SDK DFU!

#ifndef NRF_CRYPTO_BACKEND_NRF_SW_HASH_LITTLE_ENDIAN_DIGEST_ENABLED
#define NRF_CRYPTO_BACKEND_NRF_SW_HASH_LITTLE_ENDIAN_DIGEST_ENABLED 1
#endif

// </e>

// <e> NRF_CRYPTO_BACKEND_OBERON_ENABLED - Enable the Oberon backend

// <i> The Oberon backend
//==========================================================
#ifndef NRF_CRYPTO_BACKEND_OBERON_ENABLED
#define NRF_CRYPTO_BACKEND_OBERON_ENABLED 0
#endif
// <q> NRF_CRYPTO_BACKEND_OBERON_CHACHA_POLY_ENABLED  - Enable the CHACHA-POLY mode using Oberon.
 

#ifndef NRF_CRYPTO_BACKEND_OBERON_CHACHA_POLY_ENABLED
#define NRF_CRYPTO_BACKEND_OBERON_CHACHA_POLY_ENABLED 1
#endif

// <q> NRF_CRYPTO_BACKEND_OBERON_ECC_SECP256R1_ENABLED  - Enable secp256r1 curve
 

// <i> Enable this setting if you need secp256r1 curve support using Oberon library

#ifndef NRF_CRYPTO_BACKEND_OBERON_ECC_SECP256R1_ENABLED
#define NRF_CRYPTO_BACKEND_OBERON_ECC_SECP256R1_ENABLED 1
#endif

// <q> NRF_CRYPTO_BACKEND_OBERON_ECC_CURVE25519_ENABLED  - Enable Curve25519 ECDH
 

// <i> Enable this setting if you need Curve25519 ECDH support using Oberon library

#ifndef NRF_CRYPTO_BACKEND_OBERON_ECC_CURVE25519_ENABLED
#define NRF_CRYPTO_BACKEND_OBERON_ECC_CURVE25519_ENABLED 1
#endif

// <q> NRF_CRYPTO_BACKEND_OBERON_ECC_ED25519_ENABLED  - Enable Ed25519 signature scheme
 

// <i> Enable this setting if you need Ed25519 support using Oberon library

#ifndef NRF_CRYPTO_BACKEND_OBERON_ECC_ED25519_ENABLED
#define NRF_CRYPTO_BACKEND_OBERON_ECC_ED25519_ENABLED 1
#endif

// <q> NRF_CRYPTO_BACKEND_OBERON_HASH_SHA256_ENABLED  - Oberon SHA-256 hash functionality
 

// <i> Oberon backend implementation for SHA-256.

#ifndef NRF_CRYPTO_BACKEND_OBERON_HASH_SHA256_ENABLED
#define NRF_CRYPTO_BACKEND_OBERON_HASH_SHA256_ENABLED 1
#endif

// <q> NRF_CRYPTO_BACKEND_OBERON_HASH_SHA512_ENABLED  - Oberon SHA-512 hash functionality
 

// <i> Oberon backend implementation for SHA-512.

#ifndef NRF_CRYPTO_BACKEND_OBERON_HASH_SHA512_ENABLED
#define NRF_CRYPTO_BACKEND_OBERON_HASH_SHA512_ENABLED 1
#endif

// <q> NRF_CRYPTO_BACKEND_OBERON_HMAC_SHA256_ENABLED  - Oberon HMAC using SHA-256
 

// <i> Oberon backend implementation for HMAC using SHA-256.

#ifndef NRF_CRYPTO_BACKEND_OBERON_HMAC_SHA256_ENABLED
#define NRF_CRYPTO_BACKEND_OBERON_HMAC_SHA256_ENABLED 1
#endif

// <q> NRF_CRYPTO_BACKEND_OBERON_HMAC_SHA512_ENABLED  - Oberon HMAC using SHA-512
 

// <i> Oberon backend implementation for HMAC using SHA-512.

#ifndef NRF_CRYPTO_BACKEND_OBERON_HMAC_SHA512_ENABLED
#define NRF_CRYPTO_BACKEND_OBERON_HMAC_SHA512_ENABLED 1
#endif

// </e>

// </e>

// <h> nrf_crypto_rng - RNG Configuration

//==========================================================
// <q> NRF_CRYPTO_RNG_STATIC_MEMORY_BUFFERS_ENABLED  - Use static memory buffers for context and temporary init buffer.
 

// <i> Always recommended when using the nRF HW RNG as the context and temporary buffers are small. Consider disabling if using the CC310 RNG in a RAM constrained application. In this case, memory must be provided to nrf_crypto_rng_init, or it can be allocated internally provided that NRF_CRYPTO_ALLOCATOR does not allocate memory on the stack.

#ifndef NRF_CRYPTO_RNG_STATIC_MEMORY_BUFFERS_ENABLED
#define NRF_CRYPTO_RNG_STATIC_MEMORY_BUFFERS_ENABLED 1
#endif

// <q> NRF_CRYPTO_RNG_AUTO_INIT_ENABLED  - Initialize the RNG module automatically when nrf_crypto is initialized.
 

// <i> Automatic initialization is only supported with static or internally allocated context and temporary memory.

#ifndef NRF_CRYPTO_RNG_AUTO_INIT_ENABLED
#define NRF_CRYPTO_RNG_AUTO_INIT_ENABLED 1
#endif

// </h> 
//==========================================================

// </h> 
//==========================================================

// <h> nRF_DFU 

//==========================================================
// <h> nrf_dfu - Device Firmware Upgrade

//==========================================================
// <h> DFU transport 

//==========================================================
// <e> NRF_DFU_TRANSPORT_BLE - BLE transport settings
//==========================================================
#ifndef NRF_DFU_TRANSPORT_BLE
#define NRF_DFU_TRANSPORT_BLE 1
#endif
// <s> NRF_DFU_BLE_ADV_NAME - Default advertising name.
/**
 * Device ID is being used instead of Device name for advertisement
#ifndef NRF_DFU_BLE_ADV_NAME
#define NRF_DFU_BLE_ADV_NAME "IoTReadyDFU"
#endif
 */

// <h> BLE DFU security 

//==========================================================
// <q> NRF_DFU_BLE_REQUIRES_BONDS  - Require bond with peer.
 

#ifndef NRF_DFU_BLE_REQUIRES_BONDS
#define NRF_DFU_BLE_REQUIRES_BONDS 0
#endif

// </h> 
//==========================================================

// <h> BLE DFU connection 

//==========================================================
// <o> NRF_DFU_BLE_MIN_CONN_INTERVAL - Minimum connection interval (units). 
// <i> Minimum GAP connection interval, in 1.25 ms units.

#ifndef NRF_DFU_BLE_MIN_CONN_INTERVAL
#define NRF_DFU_BLE_MIN_CONN_INTERVAL 12
#endif

// <o> NRF_DFU_BLE_MAX_CONN_INTERVAL - Maximum connection interval (units). 
// <i> Maximum GAP connection interval, in 1.25 ms units.

#ifndef NRF_DFU_BLE_MAX_CONN_INTERVAL
#define NRF_DFU_BLE_MAX_CONN_INTERVAL 12
#endif

// <o> NRF_DFU_BLE_CONN_SUP_TIMEOUT_MS - Supervision timeout (ms). 
// <i> GAP connection supervision timeout, in milliseconds.

#ifndef NRF_DFU_BLE_CONN_SUP_TIMEOUT_MS
#define NRF_DFU_BLE_CONN_SUP_TIMEOUT_MS 6000
#endif

// </h> 
//==========================================================

// <h> BLE DFU buffers 

//==========================================================
// <e> NRF_DFU_BLE_BUFFERS_OVERRIDE 

// <i> Check this option to override the default number of buffers.
//==========================================================
#ifndef NRF_DFU_BLE_BUFFERS_OVERRIDE
#define NRF_DFU_BLE_BUFFERS_OVERRIDE 0
#endif
// <o> NRF_DFU_BLE_BUFFERS - Number of buffers in the BLE transport. 
// <i> Number of buffers to store incoming data while it is being written to flash.
// <i> Reduce this value to save RAM. If this value is too low, the DFU process will fail.

#ifndef NRF_DFU_BLE_BUFFERS
#define NRF_DFU_BLE_BUFFERS 8
#endif

// </e>

// </h> 
//==========================================================

// </e>

// </h> 
//==========================================================

// <h> DFU protocol 

//==========================================================
// <q> NRF_DFU_PROTOCOL_FW_VERSION_MSG  - Firmware version message support.
 

// <i> Firmware version message support.
// <i> If disabled, firmware version requests will return NRF_DFU_RES_CODE_OP_CODE_NOT_SUPPORTED.

#ifndef NRF_DFU_PROTOCOL_FW_VERSION_MSG
#define NRF_DFU_PROTOCOL_FW_VERSION_MSG 1
#endif

// <q> NRF_DFU_PROTOCOL_VERSION_MSG  - Protocol version message support.
 

// <i> Protocol version message support.
// <i> If disabled, protocol version requests will return NRF_DFU_RES_CODE_OP_CODE_NOT_SUPPORTED.

#ifndef NRF_DFU_PROTOCOL_VERSION_MSG
#define NRF_DFU_PROTOCOL_VERSION_MSG 1
#endif

// </h> 
//==========================================================

// <h> DFU security 

//==========================================================
// <q> NRF_DFU_APP_DOWNGRADE_PREVENTION  - Check the firmware version and SoftDevice requirements of application (and SoftDevice) updates.
 

// <i> Whether to check the incoming version against the version of the existing app and/or
// <i> the incoming SoftDevice requirements against the existing SoftDevice.
// <i> This applies to application updates, and possibly to SoftDevice updates.
// <i> Disabling this causes the checks to always ignore the incoming firmware version and
// <i> to ignore the SoftDevice requirements if the first requirement is 0.
// <i> This does not apply the bootloader updates. If the bootloader depends on the SoftDevice
// <i> e.g. for BLE transport, this does not apply to SoftDevice updates.
// <i> See @ref lib_bootloader_dfu_validation for more information.
// <i> When signed updates are required, version checking should always be enabled.

#ifndef NRF_DFU_APP_DOWNGRADE_PREVENTION
#define NRF_DFU_APP_DOWNGRADE_PREVENTION 1
#endif

// <q> NRF_DFU_FORCE_DUAL_BANK_APP_UPDATES  - Accept only dual-bank application updates.
 

// <i> If not enabled then if there is not enough space to perform dual-bank update
// <i> application is deleted and single-bank update is performed. In case it is considered
// <i> security concern user can prefer to discard update request rather than overwrite
// <i> current application.

#ifndef NRF_DFU_FORCE_DUAL_BANK_APP_UPDATES
#define NRF_DFU_FORCE_DUAL_BANK_APP_UPDATES 0
#endif

// <o> NRF_DFU_HW_VERSION - Device hardware version. 
// <i> This is used to determine if given update is targeting the device.
// <i> It is checked against the hw_version value in the init packet
/**
 * Defined in ../../boards/dfu_boards.h
#ifndef NRF_DFU_HW_VERSION
#define NRF_DFU_HW_VERSION 104
#endif
*/
// <q> NRF_DFU_REQUIRE_SIGNED_APP_UPDATE  - Require a valid signature to update the application or SoftDevice.
 

#ifndef NRF_DFU_REQUIRE_SIGNED_APP_UPDATE
#define NRF_DFU_REQUIRE_SIGNED_APP_UPDATE 1
#endif

// <q> NRF_DFU_SINGLE_BANK_APP_UPDATES  - Place the application and the SoftDevice directly where they are supposed to be.
 

// <i> Note that this creates security concerns when signing and  version checks
// <i> are enabled. An attacker will be able to delete (but not replace)
// <i> the current app or SoftDevice without knowing the signature key.

#ifndef NRF_DFU_SINGLE_BANK_APP_UPDATES
#define NRF_DFU_SINGLE_BANK_APP_UPDATES 0
#endif

// </h> 
//==========================================================

// <h> Misc DFU settings 

//==========================================================
// <q> NRF_DFU_SAVE_PROGRESS_IN_FLASH  - Save DFU progress in flash.
 

// <i> Save DFU progress to flash so that it can be resumed if interrupted, instead of being restarted.
// <i> Keep this setting disabled to maximize transfer speed and minimize flash wear.
// <i> The init packet is always saved in flash, regardless of this setting.

#ifndef NRF_DFU_SAVE_PROGRESS_IN_FLASH
#define NRF_DFU_SAVE_PROGRESS_IN_FLASH 0
#endif

// </h> 
//==========================================================

// </h> 
//==========================================================

// </h> 
//==========================================================

// <h> nRF_Libraries 

//==========================================================
// <e> APP_SCHEDULER_ENABLED - app_scheduler - Events scheduler
//==========================================================
#ifndef APP_SCHEDULER_ENABLED
#define APP_SCHEDULER_ENABLED 1
#endif
// <q> APP_SCHEDULER_WITH_PAUSE  - Enabling pause feature
 

#ifndef APP_SCHEDULER_WITH_PAUSE
#define APP_SCHEDULER_WITH_PAUSE 0
#endif

// <q> APP_SCHEDULER_WITH_PROFILER  - Enabling scheduler profiling
 

#ifndef APP_SCHEDULER_WITH_PROFILER
#define APP_SCHEDULER_WITH_PROFILER 0
#endif

// </e>

// <e> APP_TIMER_ENABLED - app_timer - Application timer functionality
//==========================================================
#ifndef APP_TIMER_ENABLED
#define APP_TIMER_ENABLED 1
#endif
// <o> APP_TIMER_CONFIG_RTC_FREQUENCY  - Configure RTC prescaler.
 
// <0=> 32768 Hz 
// <1=> 16384 Hz 
// <3=> 8192 Hz 
// <7=> 4096 Hz 
// <15=> 2048 Hz 
// <31=> 1024 Hz 

#ifndef APP_TIMER_CONFIG_RTC_FREQUENCY
#define APP_TIMER_CONFIG_RTC_FREQUENCY 0
#endif

// <o> APP_TIMER_CONFIG_IRQ_PRIORITY  - Interrupt priority
 

// <i> Priorities 0,2 (nRF51) and 0,1,4,5 (nRF52) are reserved for SoftDevice
// <0=> 0 (highest) 
// <1=> 1 
// <2=> 2 
// <3=> 3 
// <4=> 4 
// <5=> 5 
// <6=> 6 
// <7=> 7 

#ifndef APP_TIMER_CONFIG_IRQ_PRIORITY
#define APP_TIMER_CONFIG_IRQ_PRIORITY 7
#endif

// <o> APP_TIMER_CONFIG_OP_QUEUE_SIZE - Capacity of timer requests queue. 
// <i> Size of the queue depends on how many timers are used
// <i> in the system, how often timers are started and overall
// <i> system latency. If queue size is too small app_timer calls
// <i> will fail.

#ifndef APP_TIMER_CONFIG_OP_QUEUE_SIZE
#define APP_TIMER_CONFIG_OP_QUEUE_SIZE 10
#endif

// <q> APP_TIMER_CONFIG_USE_SCHEDULER  - Enable scheduling app_timer events to app_scheduler
 

#ifndef APP_TIMER_CONFIG_USE_SCHEDULER
#define APP_TIMER_CONFIG_USE_SCHEDULER 0
#endif

// <q> APP_TIMER_KEEPS_RTC_ACTIVE  - Enable RTC always on
 

// <i> If option is enabled RTC is kept running even if there is no active timers.
// <i> This option can be used when app_timer is used for timestamping.

#ifndef APP_TIMER_KEEPS_RTC_ACTIVE
#define APP_TIMER_KEEPS_RTC_ACTIVE 0
#endif

// <h> App Timer Legacy configuration - Legacy configuration.

//==========================================================
// <q> APP_TIMER_WITH_PROFILER  - Enable app_timer profiling
 

#ifndef APP_TIMER_WITH_PROFILER
#define APP_TIMER_WITH_PROFILER 0
#endif

// <q> APP_TIMER_CONFIG_SWI_NUMBER  - Configure SWI instance used.
 

#ifndef APP_TIMER_CONFIG_SWI_NUMBER
#define APP_TIMER_CONFIG_SWI_NUMBER 0
#endif

// </h> 
//==========================================================

// </e>

// <q> CRC32_ENABLED  - crc32 - CRC32 calculation routines
 

#ifndef CRC32_ENABLED
#define CRC32_ENABLED 1
#endif

// <e> MEM_MANAGER_ENABLED - mem_manager - Dynamic memory allocator
//==========================================================
#ifndef MEM_MANAGER_ENABLED
#define MEM_MANAGER_ENABLED 1
#endif
// <o> MEMORY_MANAGER_SMALL_BLOCK_COUNT - Size of each memory blocks identified as 'small' block.  <0-255> 


#ifndef MEMORY_MANAGER_SMALL_BLOCK_COUNT
#define MEMORY_MANAGER_SMALL_BLOCK_COUNT 1
#endif

// <o> MEMORY_MANAGER_SMALL_BLOCK_SIZE -  Size of each memory blocks identified as 'small' block. 
// <i>  Size of each memory blocks identified as 'small' block. Memory block are recommended to be word-sized.

#ifndef MEMORY_MANAGER_SMALL_BLOCK_SIZE
#define MEMORY_MANAGER_SMALL_BLOCK_SIZE 32
#endif

// <o> MEMORY_MANAGER_MEDIUM_BLOCK_COUNT - Size of each memory blocks identified as 'medium' block.  <0-255> 


#ifndef MEMORY_MANAGER_MEDIUM_BLOCK_COUNT
#define MEMORY_MANAGER_MEDIUM_BLOCK_COUNT 0
#endif

// <o> MEMORY_MANAGER_MEDIUM_BLOCK_SIZE -  Size of each memory blocks identified as 'medium' block. 
// <i>  Size of each memory blocks identified as 'medium' block. Memory block are recommended to be word-sized.

#ifndef MEMORY_MANAGER_MEDIUM_BLOCK_SIZE
#define MEMORY_MANAGER_MEDIUM_BLOCK_SIZE 256
#endif

// <o> MEMORY_MANAGER_LARGE_BLOCK_COUNT - Size of each memory blocks identified as 'large' block.  <0-255> 


#ifndef MEMORY_MANAGER_LARGE_BLOCK_COUNT
#define MEMORY_MANAGER_LARGE_BLOCK_COUNT 0
#endif

// <o> MEMORY_MANAGER_LARGE_BLOCK_SIZE -  Size of each memory blocks identified as 'large' block. 
// <i>  Size of each memory blocks identified as 'large' block. Memory block are recommended to be word-sized.

#ifndef MEMORY_MANAGER_LARGE_BLOCK_SIZE
#define MEMORY_MANAGER_LARGE_BLOCK_SIZE 256
#endif

// <o> MEMORY_MANAGER_XLARGE_BLOCK_COUNT - Size of each memory blocks identified as 'extra large' block.  <0-255> 


#ifndef MEMORY_MANAGER_XLARGE_BLOCK_COUNT
#define MEMORY_MANAGER_XLARGE_BLOCK_COUNT 0
#endif

// <o> MEMORY_MANAGER_XLARGE_BLOCK_SIZE -  Size of each memory blocks identified as 'extra large' block. 
// <i>  Size of each memory blocks identified as 'extra large' block. Memory block are recommended to be word-sized.

#ifndef MEMORY_MANAGER_XLARGE_BLOCK_SIZE
#define MEMORY_MANAGER_XLARGE_BLOCK_SIZE 1320
#endif

// <o> MEMORY_MANAGER_XXLARGE_BLOCK_COUNT - Size of each memory blocks identified as 'extra extra large' block.  <0-255> 


#ifndef MEMORY_MANAGER_XXLARGE_BLOCK_COUNT
#define MEMORY_MANAGER_XXLARGE_BLOCK_COUNT 0
#endif

// <o> MEMORY_MANAGER_XXLARGE_BLOCK_SIZE -  Size of each memory blocks identified as 'extra extra large' block. 
// <i>  Size of each memory blocks identified as 'extra extra large' block. Memory block are recommended to be word-sized.

#ifndef MEMORY_MANAGER_XXLARGE_BLOCK_SIZE
#define MEMORY_MANAGER_XXLARGE_BLOCK_SIZE 3444
#endif

// <o> MEMORY_MANAGER_XSMALL_BLOCK_COUNT - Size of each memory blocks identified as 'extra small' block.  <0-255> 


#ifndef MEMORY_MANAGER_XSMALL_BLOCK_COUNT
#define MEMORY_MANAGER_XSMALL_BLOCK_COUNT 0
#endif

// <o> MEMORY_MANAGER_XSMALL_BLOCK_SIZE -  Size of each memory blocks identified as 'extra small' block. 
// <i>  Size of each memory blocks identified as 'extra large' block. Memory block are recommended to be word-sized.

#ifndef MEMORY_MANAGER_XSMALL_BLOCK_SIZE
#define MEMORY_MANAGER_XSMALL_BLOCK_SIZE 64
#endif

// <o> MEMORY_MANAGER_XXSMALL_BLOCK_COUNT - Size of each memory blocks identified as 'extra extra small' block.  <0-255> 


#ifndef MEMORY_MANAGER_XXSMALL_BLOCK_COUNT
#define MEMORY_MANAGER_XXSMALL_BLOCK_COUNT 0
#endif

// <o> MEMORY_MANAGER_XXSMALL_BLOCK_SIZE -  Size of each memory blocks identified as 'extra extra small' block. 
// <i>  Size of each memory blocks identified as 'extra extra small' block. Memory block are recommended to be word-sized.

#ifndef MEMORY_MANAGER_XXSMALL_BLOCK_SIZE
#define MEMORY_MANAGER_XXSMALL_BLOCK_SIZE 32
#endif

// <e> MEM_MANAGER_CONFIG_LOG_ENABLED - Enables logging in the module.
//==========================================================
#ifndef MEM_MANAGER_CONFIG_LOG_ENABLED
#define MEM_MANAGER_CONFIG_LOG_ENABLED 0
#endif
// <o> MEM_MANAGER_CONFIG_LOG_LEVEL  - Default Severity level
 
// <0=> Off 
// <1=> Error 
// <2=> Warning 
// <3=> Info 
// <4=> Debug 

#ifndef MEM_MANAGER_CONFIG_LOG_LEVEL
#define MEM_MANAGER_CONFIG_LOG_LEVEL 3
#endif

// <o> MEM_MANAGER_CONFIG_INFO_COLOR  - ANSI escape code prefix.
 
// <0=> Default 
// <1=> Black 
// <2=> Red 
// <3=> Green 
// <4=> Yellow 
// <5=> Blue 
// <6=> Magenta 
// <7=> Cyan 
// <8=> White 

#ifndef MEM_MANAGER_CONFIG_INFO_COLOR
#define MEM_MANAGER_CONFIG_INFO_COLOR 0
#endif

// <o> MEM_MANAGER_CONFIG_DEBUG_COLOR  - ANSI escape code prefix.
 
// <0=> Default 
// <1=> Black 
// <2=> Red 
// <3=> Green 
// <4=> Yellow 
// <5=> Blue 
// <6=> Magenta 
// <7=> Cyan 
// <8=> White 

#ifndef MEM_MANAGER_CONFIG_DEBUG_COLOR
#define MEM_MANAGER_CONFIG_DEBUG_COLOR 0
#endif

// </e>

// <q> MEM_MANAGER_DISABLE_API_PARAM_CHECK  - Disable API parameter checks in the module.
 

#ifndef MEM_MANAGER_DISABLE_API_PARAM_CHECK
#define MEM_MANAGER_DISABLE_API_PARAM_CHECK 0
#endif

// </e>

// <e> NRF_BALLOC_ENABLED - nrf_balloc - Block allocator module
//==========================================================
#ifndef NRF_BALLOC_ENABLED
#define NRF_BALLOC_ENABLED 1
#endif
// <e> NRF_BALLOC_CONFIG_DEBUG_ENABLED - Enables debug mode in the module.
//==========================================================
#ifndef NRF_BALLOC_CONFIG_DEBUG_ENABLED
#define NRF_BALLOC_CONFIG_DEBUG_ENABLED 0
#endif
// <o> NRF_BALLOC_CONFIG_HEAD_GUARD_WORDS - Number of words used as head guard.  <0-255> 


#ifndef NRF_BALLOC_CONFIG_HEAD_GUARD_WORDS
#define NRF_BALLOC_CONFIG_HEAD_GUARD_WORDS 1
#endif

// <o> NRF_BALLOC_CONFIG_TAIL_GUARD_WORDS - Number of words used as tail guard.  <0-255> 


#ifndef NRF_BALLOC_CONFIG_TAIL_GUARD_WORDS
#define NRF_BALLOC_CONFIG_TAIL_GUARD_WORDS 1
#endif

// <q> NRF_BALLOC_CONFIG_BASIC_CHECKS_ENABLED  - Enables basic checks in this module.
 

#ifndef NRF_BALLOC_CONFIG_BASIC_CHECKS_ENABLED
#define NRF_BALLOC_CONFIG_BASIC_CHECKS_ENABLED 0
#endif

// <q> NRF_BALLOC_CONFIG_DOUBLE_FREE_CHECK_ENABLED  - Enables double memory free check in this module.
 

#ifndef NRF_BALLOC_CONFIG_DOUBLE_FREE_CHECK_ENABLED
#define NRF_BALLOC_CONFIG_DOUBLE_FREE_CHECK_ENABLED 0
#endif

// <q> NRF_BALLOC_CONFIG_DATA_TRASHING_CHECK_ENABLED  - Enables free memory corruption check in this module.
 

#ifndef NRF_BALLOC_CONFIG_DATA_TRASHING_CHECK_ENABLED
#define NRF_BALLOC_CONFIG_DATA_TRASHING_CHECK_ENABLED 0
#endif

// <q> NRF_BALLOC_CLI_CMDS  - Enable CLI commands specific to the module
 

#ifndef NRF_BALLOC_CLI_CMDS
#define NRF_BALLOC_CLI_CMDS 0
#endif

// </e>

// </e>

// <e> NRF_FSTORAGE_ENABLED - nrf_fstorage - Flash abstraction library
//==========================================================
#ifndef NRF_FSTORAGE_ENABLED
#define NRF_FSTORAGE_ENABLED 1
#endif
// <h> nrf_fstorage - Common settings

// <i> Common settings to all fstorage implementations
//==========================================================
// <q> NRF_FSTORAGE_PARAM_CHECK_DISABLED  - Disable user input validation
 

// <i> If selected, use ASSERT to validate user input.
// <i> This effectively removes user input validation in production code.
// <i> Recommended setting: OFF, only enable this setting if size is a major concern.

#ifndef NRF_FSTORAGE_PARAM_CHECK_DISABLED
#define NRF_FSTORAGE_PARAM_CHECK_DISABLED 1
#endif

// </h> 
//==========================================================

// <h> nrf_fstorage_sd - Implementation using the SoftDevice

// <i> Configuration options for the fstorage implementation using the SoftDevice
//==========================================================
// <o> NRF_FSTORAGE_SD_QUEUE_SIZE - Size of the internal queue of operations 
// <i> Increase this value if API calls frequently return the error @ref NRF_ERROR_NO_MEM.

#ifndef NRF_FSTORAGE_SD_QUEUE_SIZE
#define NRF_FSTORAGE_SD_QUEUE_SIZE 16
#endif

// <o> NRF_FSTORAGE_SD_MAX_RETRIES - Maximum number of attempts at executing an operation when the SoftDevice is busy 
// <i> Increase this value if events frequently return the @ref NRF_ERROR_TIMEOUT error.
// <i> The SoftDevice might fail to schedule flash access due to high BLE activity.

#ifndef NRF_FSTORAGE_SD_MAX_RETRIES
#define NRF_FSTORAGE_SD_MAX_RETRIES 8
#endif

// <o> NRF_FSTORAGE_SD_MAX_WRITE_SIZE - Maximum number of bytes to be written to flash in a single operation 
// <i> This value must be a multiple of four.
// <i> Lowering this value can increase the chances of the SoftDevice being able to execute flash operations in between radio activity.
// <i> This value is bound by the maximum number of bytes that can be written to flash in a single call to @ref sd_flash_write.
// <i> That is 1024 bytes for nRF51 ICs and 4096 bytes for nRF52 ICs.

#ifndef NRF_FSTORAGE_SD_MAX_WRITE_SIZE
#define NRF_FSTORAGE_SD_MAX_WRITE_SIZE 20
#endif

// </h> 
//==========================================================

// </e>

// <q> NRF_MEMOBJ_ENABLED  - nrf_memobj - Linked memory allocator module
 

#ifndef NRF_MEMOBJ_ENABLED
#define NRF_MEMOBJ_ENABLED 0
#endif

// <e> NRF_QUEUE_ENABLED - nrf_queue - Queue module
//==========================================================
#ifndef NRF_QUEUE_ENABLED
#define NRF_QUEUE_ENABLED 0
#endif
// <q> NRF_QUEUE_CLI_CMDS  - Enable CLI commands specific to the module
 

#ifndef NRF_QUEUE_CLI_CMDS
#define NRF_QUEUE_CLI_CMDS 0
#endif

// </e>

// <q> NRF_SECTION_ITER_ENABLED  - nrf_section_iter - Section iterator
 

#ifndef NRF_SECTION_ITER_ENABLED
#define NRF_SECTION_ITER_ENABLED 1
#endif

// <q> NRF_SORTLIST_ENABLED  - nrf_sortlist - Sorted list
 

#ifndef NRF_SORTLIST_ENABLED
#define NRF_SORTLIST_ENABLED 1
#endif

// <q> NRF_STRERROR_ENABLED  - nrf_strerror - Library for converting error code to string.
 

#ifndef NRF_STRERROR_ENABLED
#define NRF_STRERROR_ENABLED 1
#endif

// </h> 
//==========================================================

// <h> nRF_Log 

//==========================================================
// <h> nrf_log - Logger

//==========================================================
// <e> NRF_LOG_ENABLED - Logging module for nRF5 SDK
//==========================================================
#ifndef NRF_LOG_ENABLED
#define NRF_LOG_ENABLED 0
#endif
// <e> NRF_LOG_USES_COLORS - If enabled then ANSI escape code for colors is prefixed to every string
//==========================================================
#ifndef NRF_LOG_USES_COLORS
#define NRF_LOG_USES_COLORS 0
#endif
// <o> NRF_LOG_COLOR_DEFAULT  - ANSI escape code prefix.
 
// <0=> Default 
// <1=> Black 
// <2=> Red 
// <3=> Green 
// <4=> Yellow 
// <5=> Blue 
// <6=> Magenta 
// <7=> Cyan 
// <8=> White 

#ifndef NRF_LOG_COLOR_DEFAULT
#define NRF_LOG_COLOR_DEFAULT 0
#endif

// <o> NRF_LOG_ERROR_COLOR  - ANSI escape code prefix.
 
// <0=> Default 
// <1=> Black 
// <2=> Red 
// <3=> Green 
// <4=> Yellow 
// <5=> Blue 
// <6=> Magenta 
// <7=> Cyan 
// <8=> White 

#ifndef NRF_LOG_ERROR_COLOR
#define NRF_LOG_ERROR_COLOR 2
#endif

// <o> NRF_LOG_WARNING_COLOR  - ANSI escape code prefix.
 
// <0=> Default 
// <1=> Black 
// <2=> Red 
// <3=> Green 
// <4=> Yellow 
// <5=> Blue 
// <6=> Magenta 
// <7=> Cyan 
// <8=> White 

#ifndef NRF_LOG_WARNING_COLOR
#define NRF_LOG_WARNING_COLOR 4
#endif

// </e>

// <o> NRF_LOG_DEFAULT_LEVEL  - Default Severity level
 
// <0=> Off 
// <1=> Error 
// <2=> Warning 
// <3=> Info 
// <4=> Debug 

#ifndef NRF_LOG_DEFAULT_LEVEL
#define NRF_LOG_DEFAULT_LEVEL 3
#endif

// <q> NRF_LOG_DEFERRED  - Enable deffered logger.
 

// <i> Log data is buffered and can be processed in idle.

#ifndef NRF_LOG_DEFERRED
#define NRF_LOG_DEFERRED 1
#endif

// <o> NRF_LOG_BUFSIZE  - Size of the buffer for storing logs (in bytes).
 

// <i> Must be power of 2 and multiple of 4.
// <i> If NRF_LOG_DEFERRED = 0 then buffer size can be reduced to minimum.
// <128=> 128 
// <256=> 256 
// <512=> 512 
// <1024=> 1024 
// <2048=> 2048 
// <4096=> 4096 
// <8192=> 8192 
// <16384=> 16384 

#ifndef NRF_LOG_BUFSIZE
#define NRF_LOG_BUFSIZE 1024
#endif

// <q> NRF_LOG_ALLOW_OVERFLOW  - Configures behavior when circular buffer is full.
 

// <i> If set then oldest logs are overwritten. Otherwise a 
// <i> marker is injected informing about overflow.

#ifndef NRF_LOG_ALLOW_OVERFLOW
#define NRF_LOG_ALLOW_OVERFLOW 1
#endif

// <e> NRF_LOG_USES_TIMESTAMP - Enable timestamping

// <i> Function for getting the timestamp is provided by the user
//==========================================================
#ifndef NRF_LOG_USES_TIMESTAMP
#define NRF_LOG_USES_TIMESTAMP 0
#endif
// <o> NRF_LOG_TIMESTAMP_DEFAULT_FREQUENCY - Default frequency of the timestamp (in Hz) 
#ifndef NRF_LOG_TIMESTAMP_DEFAULT_FREQUENCY
#define NRF_LOG_TIMESTAMP_DEFAULT_FREQUENCY 32768
#endif

// </e>

// <q> NRF_LOG_FILTERS_ENABLED  - Enable dynamic filtering of logs.
 

#ifndef NRF_LOG_FILTERS_ENABLED
#define NRF_LOG_FILTERS_ENABLED 0
#endif

// <q> NRF_LOG_CLI_CMDS  - Enable CLI commands for the module.
 

#ifndef NRF_LOG_CLI_CMDS
#define NRF_LOG_CLI_CMDS 0
#endif

// <h> Log message pool - Configuration of log message pool

//==========================================================
// <o> NRF_LOG_MSGPOOL_ELEMENT_SIZE - Size of a single element in the pool of memory objects. 
// <i> If a small value is set, then performance of logs processing
// <i> is degraded because data is fragmented. Bigger value impacts
// <i> RAM memory utilization. The size is set to fit a message with
// <i> a timestamp and up to 2 arguments in a single memory object.

#ifndef NRF_LOG_MSGPOOL_ELEMENT_SIZE
#define NRF_LOG_MSGPOOL_ELEMENT_SIZE 20
#endif

// <o> NRF_LOG_MSGPOOL_ELEMENT_COUNT - Number of elements in the pool of memory objects 
// <i> If a small value is set, then it may lead to a deadlock
// <i> in certain cases if backend has high latency and holds
// <i> multiple messages for long time. Bigger value impacts
// <i> RAM memory usage.

#ifndef NRF_LOG_MSGPOOL_ELEMENT_COUNT
#define NRF_LOG_MSGPOOL_ELEMENT_COUNT 8
#endif

// </h> 
//==========================================================

// </e>

// <h> nrf_log module configuration 

//==========================================================
// <h> nrf_log in nRF_Core 

//==========================================================
// <e> NRF_MPU_CONFIG_LOG_ENABLED - Enables logging in the module.
//==========================================================
#ifndef NRF_MPU_CONFIG_LOG_ENABLED
#define NRF_MPU_CONFIG_LOG_ENABLED 0
#endif
// <o> NRF_MPU_CONFIG_LOG_LEVEL  - Default Severity level
 
// <0=> Off 
// <1=> Error 
// <2=> Warning 
// <3=> Info 
// <4=> Debug 

#ifndef NRF_MPU_CONFIG_LOG_LEVEL
#define NRF_MPU_CONFIG_LOG_LEVEL 3
#endif

// <o> NRF_MPU_CONFIG_INFO_COLOR  - ANSI escape code prefix.
 
// <0=> Default 
// <1=> Black 
// <2=> Red 
// <3=> Green 
// <4=> Yellow 
// <5=> Blue 
// <6=> Magenta 
// <7=> Cyan 
// <8=> White 

#ifndef NRF_MPU_CONFIG_INFO_COLOR
#define NRF_MPU_CONFIG_INFO_COLOR 0
#endif

// <o> NRF_MPU_CONFIG_DEBUG_COLOR  - ANSI escape code prefix.
 
// <0=> Default 
// <1=> Black 
// <2=> Red 
// <3=> Green 
// <4=> Yellow 
// <5=> Blue 
// <6=> Magenta 
// <7=> Cyan 
// <8=> White 

#ifndef NRF_MPU_CONFIG_DEBUG_COLOR
#define NRF_MPU_CONFIG_DEBUG_COLOR 0
#endif

// </e>

// <e> NRF_STACK_GUARD_CONFIG_LOG_ENABLED - Enables logging in the module.
//==========================================================
#ifndef NRF_STACK_GUARD_CONFIG_LOG_ENABLED
#define NRF_STACK_GUARD_CONFIG_LOG_ENABLED 0
#endif
// <o> NRF_STACK_GUARD_CONFIG_LOG_LEVEL  - Default Severity level
 
// <0=> Off 
// <1=> Error 
// <2=> Warning 
// <3=> Info 
// <4=> Debug 

#ifndef NRF_STACK_GUARD_CONFIG_LOG_LEVEL
#define NRF_STACK_GUARD_CONFIG_LOG_LEVEL 3
#endif

// <o> NRF_STACK_GUARD_CONFIG_INFO_COLOR  - ANSI escape code prefix.
 
// <0=> Default 
// <1=> Black 
// <2=> Red 
// <3=> Green 
// <4=> Yellow 
// <5=> Blue 
// <6=> Magenta 
// <7=> Cyan 
// <8=> White 

#ifndef NRF_STACK_GUARD_CONFIG_INFO_COLOR
#define NRF_STACK_GUARD_CONFIG_INFO_COLOR 0
#endif

// <o> NRF_STACK_GUARD_CONFIG_DEBUG_COLOR  - ANSI escape code prefix.
 
// <0=> Default 
// <1=> Black 
// <2=> Red 
// <3=> Green 
// <4=> Yellow 
// <5=> Blue 
// <6=> Magenta 
// <7=> Cyan 
// <8=> White 

#ifndef NRF_STACK_GUARD_CONFIG_DEBUG_COLOR
#define NRF_STACK_GUARD_CONFIG_DEBUG_COLOR 0
#endif

// </e>

// <e> TASK_MANAGER_CONFIG_LOG_ENABLED - Enables logging in the module.
//==========================================================
#ifndef TASK_MANAGER_CONFIG_LOG_ENABLED
#define TASK_MANAGER_CONFIG_LOG_ENABLED 0
#endif
// <o> TASK_MANAGER_CONFIG_LOG_LEVEL  - Default Severity level
 
// <0=> Off 
// <1=> Error 
// <2=> Warning 
// <3=> Info 
// <4=> Debug 

#ifndef TASK_MANAGER_CONFIG_LOG_LEVEL
#define TASK_MANAGER_CONFIG_LOG_LEVEL 3
#endif

// <o> TASK_MANAGER_CONFIG_INFO_COLOR  - ANSI escape code prefix.
 
// <0=> Default 
// <1=> Black 
// <2=> Red 
// <3=> Green 
// <4=> Yellow 
// <5=> Blue 
// <6=> Magenta 
// <7=> Cyan 
// <8=> White 

#ifndef TASK_MANAGER_CONFIG_INFO_COLOR
#define TASK_MANAGER_CONFIG_INFO_COLOR 0
#endif

// <o> TASK_MANAGER_CONFIG_DEBUG_COLOR  - ANSI escape code prefix.
 
// <0=> Default 
// <1=> Black 
// <2=> Red 
// <3=> Green 
// <4=> Yellow 
// <5=> Blue 
// <6=> Magenta 
// <7=> Cyan 
// <8=> White 

#ifndef TASK_MANAGER_CONFIG_DEBUG_COLOR
#define TASK_MANAGER_CONFIG_DEBUG_COLOR 0
#endif

// </e>

// </h> 
//==========================================================

// <h> nrf_log in nRF_Drivers 

//==========================================================
// <e> CLOCK_CONFIG_LOG_ENABLED - Enables logging in the module.
//==========================================================
#ifndef CLOCK_CONFIG_LOG_ENABLED
#define CLOCK_CONFIG_LOG_ENABLED 0
#endif
// <o> CLOCK_CONFIG_LOG_LEVEL  - Default Severity level
 
// <0=> Off 
// <1=> Error 
// <2=> Warning 
// <3=> Info 
// <4=> Debug 

#ifndef CLOCK_CONFIG_LOG_LEVEL
#define CLOCK_CONFIG_LOG_LEVEL 3
#endif

// <o> CLOCK_CONFIG_INFO_COLOR  - ANSI escape code prefix.
 
// <0=> Default 
// <1=> Black 
// <2=> Red 
// <3=> Green 
// <4=> Yellow 
// <5=> Blue 
// <6=> Magenta 
// <7=> Cyan 
// <8=> White 

#ifndef CLOCK_CONFIG_INFO_COLOR
#define CLOCK_CONFIG_INFO_COLOR 0
#endif

// <o> CLOCK_CONFIG_DEBUG_COLOR  - ANSI escape code prefix.
 
// <0=> Default 
// <1=> Black 
// <2=> Red 
// <3=> Green 
// <4=> Yellow 
// <5=> Blue 
// <6=> Magenta 
// <7=> Cyan 
// <8=> White 

#ifndef CLOCK_CONFIG_DEBUG_COLOR
#define CLOCK_CONFIG_DEBUG_COLOR 0
#endif

// </e>

// <e> COMP_CONFIG_LOG_ENABLED - Enables logging in the module.
//==========================================================
#ifndef COMP_CONFIG_LOG_ENABLED
#define COMP_CONFIG_LOG_ENABLED 0
#endif
// <o> COMP_CONFIG_LOG_LEVEL  - Default Severity level
 
// <0=> Off 
// <1=> Error 
// <2=> Warning 
// <3=> Info 
// <4=> Debug 

#ifndef COMP_CONFIG_LOG_LEVEL
#define COMP_CONFIG_LOG_LEVEL 3
#endif

// <o> COMP_CONFIG_INFO_COLOR  - ANSI escape code prefix.
 
// <0=> Default 
// <1=> Black 
// <2=> Red 
// <3=> Green 
// <4=> Yellow 
// <5=> Blue 
// <6=> Magenta 
// <7=> Cyan 
// <8=> White 

#ifndef COMP_CONFIG_INFO_COLOR
#define COMP_CONFIG_INFO_COLOR 0
#endif

// <o> COMP_CONFIG_DEBUG_COLOR  - ANSI escape code prefix.
 
// <0=> Default 
// <1=> Black 
// <2=> Red 
// <3=> Green 
// <4=> Yellow 
// <5=> Blue 
// <6=> Magenta 
// <7=> Cyan 
// <8=> White 

#ifndef COMP_CONFIG_DEBUG_COLOR
#define COMP_CONFIG_DEBUG_COLOR 0
#endif

// </e>

// <e> GPIOTE_CONFIG_LOG_ENABLED - Enables logging in the module.
//==========================================================
#ifndef GPIOTE_CONFIG_LOG_ENABLED
#define GPIOTE_CONFIG_LOG_ENABLED 0
#endif
// <o> GPIOTE_CONFIG_LOG_LEVEL  - Default Severity level
 
// <0=> Off 
// <1=> Error 
// <2=> Warning 
// <3=> Info 
// <4=> Debug 

#ifndef GPIOTE_CONFIG_LOG_LEVEL
#define GPIOTE_CONFIG_LOG_LEVEL 3
#endif

// <o> GPIOTE_CONFIG_INFO_COLOR  - ANSI escape code prefix.
 
// <0=> Default 
// <1=> Black 
// <2=> Red 
// <3=> Green 
// <4=> Yellow 
// <5=> Blue 
// <6=> Magenta 
// <7=> Cyan 
// <8=> White 

#ifndef GPIOTE_CONFIG_INFO_COLOR
#define GPIOTE_CONFIG_INFO_COLOR 0
#endif

// <o> GPIOTE_CONFIG_DEBUG_COLOR  - ANSI escape code prefix.
 
// <0=> Default 
// <1=> Black 
// <2=> Red 
// <3=> Green 
// <4=> Yellow 
// <5=> Blue 
// <6=> Magenta 
// <7=> Cyan 
// <8=> White 

#ifndef GPIOTE_CONFIG_DEBUG_COLOR
#define GPIOTE_CONFIG_DEBUG_COLOR 0
#endif

// </e>

// <e> LPCOMP_CONFIG_LOG_ENABLED - Enables logging in the module.
//==========================================================
#ifndef LPCOMP_CONFIG_LOG_ENABLED
#define LPCOMP_CONFIG_LOG_ENABLED 0
#endif
// <o> LPCOMP_CONFIG_LOG_LEVEL  - Default Severity level
 
// <0=> Off 
// <1=> Error 
// <2=> Warning 
// <3=> Info 
// <4=> Debug 

#ifndef LPCOMP_CONFIG_LOG_LEVEL
#define LPCOMP_CONFIG_LOG_LEVEL 3
#endif

// <o> LPCOMP_CONFIG_INFO_COLOR  - ANSI escape code prefix.
 
// <0=> Default 
// <1=> Black 
// <2=> Red 
// <3=> Green 
// <4=> Yellow 
// <5=> Blue 
// <6=> Magenta 
// <7=> Cyan 
// <8=> White 

#ifndef LPCOMP_CONFIG_INFO_COLOR
#define LPCOMP_CONFIG_INFO_COLOR 0
#endif

// <o> LPCOMP_CONFIG_DEBUG_COLOR  - ANSI escape code prefix.
 
// <0=> Default 
// <1=> Black 
// <2=> Red 
// <3=> Green 
// <4=> Yellow 
// <5=> Blue 
// <6=> Magenta 
// <7=> Cyan 
// <8=> White 

#ifndef LPCOMP_CONFIG_DEBUG_COLOR
#define LPCOMP_CONFIG_DEBUG_COLOR 0
#endif

// </e>

// <e> PDM_CONFIG_LOG_ENABLED - Enables logging in the module.
//==========================================================
#ifndef PDM_CONFIG_LOG_ENABLED
#define PDM_CONFIG_LOG_ENABLED 0
#endif
// <o> PDM_CONFIG_LOG_LEVEL  - Default Severity level
 
// <0=> Off 
// <1=> Error 
// <2=> Warning 
// <3=> Info 
// <4=> Debug 

#ifndef PDM_CONFIG_LOG_LEVEL
#define PDM_CONFIG_LOG_LEVEL 3
#endif

// <o> PDM_CONFIG_INFO_COLOR  - ANSI escape code prefix.
 
// <0=> Default 
// <1=> Black 
// <2=> Red 
// <3=> Green 
// <4=> Yellow 
// <5=> Blue 
// <6=> Magenta 
// <7=> Cyan 
// <8=> White 

#ifndef PDM_CONFIG_INFO_COLOR
#define PDM_CONFIG_INFO_COLOR 0
#endif

// <o> PDM_CONFIG_DEBUG_COLOR  - ANSI escape code prefix.
 
// <0=> Default 
// <1=> Black 
// <2=> Red 
// <3=> Green 
// <4=> Yellow 
// <5=> Blue 
// <6=> Magenta 
// <7=> Cyan 
// <8=> White 

#ifndef PDM_CONFIG_DEBUG_COLOR
#define PDM_CONFIG_DEBUG_COLOR 0
#endif

// </e>

// <e> PPI_CONFIG_LOG_ENABLED - Enables logging in the module.
//==========================================================
#ifndef PPI_CONFIG_LOG_ENABLED
#define PPI_CONFIG_LOG_ENABLED 0
#endif
// <o> PPI_CONFIG_LOG_LEVEL  - Default Severity level
 
// <0=> Off 
// <1=> Error 
// <2=> Warning 
// <3=> Info 
// <4=> Debug 

#ifndef PPI_CONFIG_LOG_LEVEL
#define PPI_CONFIG_LOG_LEVEL 3
#endif

// <o> PPI_CONFIG_INFO_COLOR  - ANSI escape code prefix.
 
// <0=> Default 
// <1=> Black 
// <2=> Red 
// <3=> Green 
// <4=> Yellow 
// <5=> Blue 
// <6=> Magenta 
// <7=> Cyan 
// <8=> White 

#ifndef PPI_CONFIG_INFO_COLOR
#define PPI_CONFIG_INFO_COLOR 0
#endif

// <o> PPI_CONFIG_DEBUG_COLOR  - ANSI escape code prefix.
 
// <0=> Default 
// <1=> Black 
// <2=> Red 
// <3=> Green 
// <4=> Yellow 
// <5=> Blue 
// <6=> Magenta 
// <7=> Cyan 
// <8=> White 

#ifndef PPI_CONFIG_DEBUG_COLOR
#define PPI_CONFIG_DEBUG_COLOR 0
#endif

// </e>

// <e> PWM_CONFIG_LOG_ENABLED - Enables logging in the module.
//==========================================================
#ifndef PWM_CONFIG_LOG_ENABLED
#define PWM_CONFIG_LOG_ENABLED 0
#endif
// <o> PWM_CONFIG_LOG_LEVEL  - Default Severity level
 
// <0=> Off 
// <1=> Error 
// <2=> Warning 
// <3=> Info 
// <4=> Debug 

#ifndef PWM_CONFIG_LOG_LEVEL
#define PWM_CONFIG_LOG_LEVEL 3
#endif

// <o> PWM_CONFIG_INFO_COLOR  - ANSI escape code prefix.
 
// <0=> Default 
// <1=> Black 
// <2=> Red 
// <3=> Green 
// <4=> Yellow 
// <5=> Blue 
// <6=> Magenta 
// <7=> Cyan 
// <8=> White 

#ifndef PWM_CONFIG_INFO_COLOR
#define PWM_CONFIG_INFO_COLOR 0
#endif

// <o> PWM_CONFIG_DEBUG_COLOR  - ANSI escape code prefix.
 
// <0=> Default 
// <1=> Black 
// <2=> Red 
// <3=> Green 
// <4=> Yellow 
// <5=> Blue 
// <6=> Magenta 
// <7=> Cyan 
// <8=> White 

#ifndef PWM_CONFIG_DEBUG_COLOR
#define PWM_CONFIG_DEBUG_COLOR 0
#endif

// </e>

// <e> QDEC_CONFIG_LOG_ENABLED - Enables logging in the module.
//==========================================================
#ifndef QDEC_CONFIG_LOG_ENABLED
#define QDEC_CONFIG_LOG_ENABLED 0
#endif
// <o> QDEC_CONFIG_LOG_LEVEL  - Default Severity level
 
// <0=> Off 
// <1=> Error 
// <2=> Warning 
// <3=> Info 
// <4=> Debug 

#ifndef QDEC_CONFIG_LOG_LEVEL
#define QDEC_CONFIG_LOG_LEVEL 3
#endif

// <o> QDEC_CONFIG_INFO_COLOR  - ANSI escape code prefix.
 
// <0=> Default 
// <1=> Black 
// <2=> Red 
// <3=> Green 
// <4=> Yellow 
// <5=> Blue 
// <6=> Magenta 
// <7=> Cyan 
// <8=> White 

#ifndef QDEC_CONFIG_INFO_COLOR
#define QDEC_CONFIG_INFO_COLOR 0
#endif

// <o> QDEC_CONFIG_DEBUG_COLOR  - ANSI escape code prefix.
 
// <0=> Default 
// <1=> Black 
// <2=> Red 
// <3=> Green 
// <4=> Yellow 
// <5=> Blue 
// <6=> Magenta 
// <7=> Cyan 
// <8=> White 

#ifndef QDEC_CONFIG_DEBUG_COLOR
#define QDEC_CONFIG_DEBUG_COLOR 0
#endif

// </e>

// <e> RNG_CONFIG_LOG_ENABLED - Enables logging in the module.
//==========================================================
#ifndef RNG_CONFIG_LOG_ENABLED
#define RNG_CONFIG_LOG_ENABLED 0
#endif
// <o> RNG_CONFIG_LOG_LEVEL  - Default Severity level
 
// <0=> Off 
// <1=> Error 
// <2=> Warning 
// <3=> Info 
// <4=> Debug 

#ifndef RNG_CONFIG_LOG_LEVEL
#define RNG_CONFIG_LOG_LEVEL 3
#endif

// <o> RNG_CONFIG_INFO_COLOR  - ANSI escape code prefix.
 
// <0=> Default 
// <1=> Black 
// <2=> Red 
// <3=> Green 
// <4=> Yellow 
// <5=> Blue 
// <6=> Magenta 
// <7=> Cyan 
// <8=> White 

#ifndef RNG_CONFIG_INFO_COLOR
#define RNG_CONFIG_INFO_COLOR 0
#endif

// <o> RNG_CONFIG_DEBUG_COLOR  - ANSI escape code prefix.
 
// <0=> Default 
// <1=> Black 
// <2=> Red 
// <3=> Green 
// <4=> Yellow 
// <5=> Blue 
// <6=> Magenta 
// <7=> Cyan 
// <8=> White 

#ifndef RNG_CONFIG_DEBUG_COLOR
#define RNG_CONFIG_DEBUG_COLOR 0
#endif

// <q> RNG_CONFIG_RANDOM_NUMBER_LOG_ENABLED  - Enables logging of random numbers.
 

#ifndef RNG_CONFIG_RANDOM_NUMBER_LOG_ENABLED
#define RNG_CONFIG_RANDOM_NUMBER_LOG_ENABLED 0
#endif

// </e>

// <e> RTC_CONFIG_LOG_ENABLED - Enables logging in the module.
//==========================================================
#ifndef RTC_CONFIG_LOG_ENABLED
#define RTC_CONFIG_LOG_ENABLED 0
#endif
// <o> RTC_CONFIG_LOG_LEVEL  - Default Severity level
 
// <0=> Off 
// <1=> Error 
// <2=> Warning 
// <3=> Info 
// <4=> Debug 

#ifndef RTC_CONFIG_LOG_LEVEL
#define RTC_CONFIG_LOG_LEVEL 3
#endif

// <o> RTC_CONFIG_INFO_COLOR  - ANSI escape code prefix.
 
// <0=> Default 
// <1=> Black 
// <2=> Red 
// <3=> Green 
// <4=> Yellow 
// <5=> Blue 
// <6=> Magenta 
// <7=> Cyan 
// <8=> White 

#ifndef RTC_CONFIG_INFO_COLOR
#define RTC_CONFIG_INFO_COLOR 0
#endif

// <o> RTC_CONFIG_DEBUG_COLOR  - ANSI escape code prefix.
 
// <0=> Default 
// <1=> Black 
// <2=> Red 
// <3=> Green 
// <4=> Yellow 
// <5=> Blue 
// <6=> Magenta 
// <7=> Cyan 
// <8=> White 

#ifndef RTC_CONFIG_DEBUG_COLOR
#define RTC_CONFIG_DEBUG_COLOR 0
#endif

// </e>

// <e> SAADC_CONFIG_LOG_ENABLED - Enables logging in the module.
//==========================================================
#ifndef SAADC_CONFIG_LOG_ENABLED
#define SAADC_CONFIG_LOG_ENABLED 0
#endif
// <o> SAADC_CONFIG_LOG_LEVEL  - Default Severity level
 
// <0=> Off 
// <1=> Error 
// <2=> Warning 
// <3=> Info 
// <4=> Debug 

#ifndef SAADC_CONFIG_LOG_LEVEL
#define SAADC_CONFIG_LOG_LEVEL 3
#endif

// <o> SAADC_CONFIG_INFO_COLOR  - ANSI escape code prefix.
 
// <0=> Default 
// <1=> Black 
// <2=> Red 
// <3=> Green 
// <4=> Yellow 
// <5=> Blue 
// <6=> Magenta 
// <7=> Cyan 
// <8=> White 

#ifndef SAADC_CONFIG_INFO_COLOR
#define SAADC_CONFIG_INFO_COLOR 0
#endif

// <o> SAADC_CONFIG_DEBUG_COLOR  - ANSI escape code prefix.
 
// <0=> Default 
// <1=> Black 
// <2=> Red 
// <3=> Green 
// <4=> Yellow 
// <5=> Blue 
// <6=> Magenta 
// <7=> Cyan 
// <8=> White 

#ifndef SAADC_CONFIG_DEBUG_COLOR
#define SAADC_CONFIG_DEBUG_COLOR 0
#endif

// </e>

// <e> SPIS_CONFIG_LOG_ENABLED - Enables logging in the module.
//==========================================================
#ifndef SPIS_CONFIG_LOG_ENABLED
#define SPIS_CONFIG_LOG_ENABLED 0
#endif
// <o> SPIS_CONFIG_LOG_LEVEL  - Default Severity level
 
// <0=> Off 
// <1=> Error 
// <2=> Warning 
// <3=> Info 
// <4=> Debug 

#ifndef SPIS_CONFIG_LOG_LEVEL
#define SPIS_CONFIG_LOG_LEVEL 3
#endif

// <o> SPIS_CONFIG_INFO_COLOR  - ANSI escape code prefix.
 
// <0=> Default 
// <1=> Black 
// <2=> Red 
// <3=> Green 
// <4=> Yellow 
// <5=> Blue 
// <6=> Magenta 
// <7=> Cyan 
// <8=> White 

#ifndef SPIS_CONFIG_INFO_COLOR
#define SPIS_CONFIG_INFO_COLOR 0
#endif

// <o> SPIS_CONFIG_DEBUG_COLOR  - ANSI escape code prefix.
 
// <0=> Default 
// <1=> Black 
// <2=> Red 
// <3=> Green 
// <4=> Yellow 
// <5=> Blue 
// <6=> Magenta 
// <7=> Cyan 
// <8=> White 

#ifndef SPIS_CONFIG_DEBUG_COLOR
#define SPIS_CONFIG_DEBUG_COLOR 0
#endif

// </e>

// <e> SPI_CONFIG_LOG_ENABLED - Enables logging in the module.
//==========================================================
#ifndef SPI_CONFIG_LOG_ENABLED
#define SPI_CONFIG_LOG_ENABLED 0
#endif
// <o> SPI_CONFIG_LOG_LEVEL  - Default Severity level
 
// <0=> Off 
// <1=> Error 
// <2=> Warning 
// <3=> Info 
// <4=> Debug 

#ifndef SPI_CONFIG_LOG_LEVEL
#define SPI_CONFIG_LOG_LEVEL 3
#endif

// <o> SPI_CONFIG_INFO_COLOR  - ANSI escape code prefix.
 
// <0=> Default 
// <1=> Black 
// <2=> Red 
// <3=> Green 
// <4=> Yellow 
// <5=> Blue 
// <6=> Magenta 
// <7=> Cyan 
// <8=> White 

#ifndef SPI_CONFIG_INFO_COLOR
#define SPI_CONFIG_INFO_COLOR 0
#endif

// <o> SPI_CONFIG_DEBUG_COLOR  - ANSI escape code prefix.
 
// <0=> Default 
// <1=> Black 
// <2=> Red 
// <3=> Green 
// <4=> Yellow 
// <5=> Blue 
// <6=> Magenta 
// <7=> Cyan 
// <8=> White 

#ifndef SPI_CONFIG_DEBUG_COLOR
#define SPI_CONFIG_DEBUG_COLOR 0
#endif

// </e>

// <e> TIMER_CONFIG_LOG_ENABLED - Enables logging in the module.
//==========================================================
#ifndef TIMER_CONFIG_LOG_ENABLED
#define TIMER_CONFIG_LOG_ENABLED 0
#endif
// <o> TIMER_CONFIG_LOG_LEVEL  - Default Severity level
 
// <0=> Off 
// <1=> Error 
// <2=> Warning 
// <3=> Info 
// <4=> Debug 

#ifndef TIMER_CONFIG_LOG_LEVEL
#define TIMER_CONFIG_LOG_LEVEL 3
#endif

// <o> TIMER_CONFIG_INFO_COLOR  - ANSI escape code prefix.
 
// <0=> Default 
// <1=> Black 
// <2=> Red 
// <3=> Green 
// <4=> Yellow 
// <5=> Blue 
// <6=> Magenta 
// <7=> Cyan 
// <8=> White 

#ifndef TIMER_CONFIG_INFO_COLOR
#define TIMER_CONFIG_INFO_COLOR 0
#endif

// <o> TIMER_CONFIG_DEBUG_COLOR  - ANSI escape code prefix.
 
// <0=> Default 
// <1=> Black 
// <2=> Red 
// <3=> Green 
// <4=> Yellow 
// <5=> Blue 
// <6=> Magenta 
// <7=> Cyan 
// <8=> White 

#ifndef TIMER_CONFIG_DEBUG_COLOR
#define TIMER_CONFIG_DEBUG_COLOR 0
#endif

// </e>

// <e> TWIS_CONFIG_LOG_ENABLED - Enables logging in the module.
//==========================================================
#ifndef TWIS_CONFIG_LOG_ENABLED
#define TWIS_CONFIG_LOG_ENABLED 0
#endif
// <o> TWIS_CONFIG_LOG_LEVEL  - Default Severity level
 
// <0=> Off 
// <1=> Error 
// <2=> Warning 
// <3=> Info 
// <4=> Debug 

#ifndef TWIS_CONFIG_LOG_LEVEL
#define TWIS_CONFIG_LOG_LEVEL 3
#endif

// <o> TWIS_CONFIG_INFO_COLOR  - ANSI escape code prefix.
 
// <0=> Default 
// <1=> Black 
// <2=> Red 
// <3=> Green 
// <4=> Yellow 
// <5=> Blue 
// <6=> Magenta 
// <7=> Cyan 
// <8=> White 

#ifndef TWIS_CONFIG_INFO_COLOR
#define TWIS_CONFIG_INFO_COLOR 0
#endif

// <o> TWIS_CONFIG_DEBUG_COLOR  - ANSI escape code prefix.
 
// <0=> Default 
// <1=> Black 
// <2=> Red 
// <3=> Green 
// <4=> Yellow 
// <5=> Blue 
// <6=> Magenta 
// <7=> Cyan 
// <8=> White 

#ifndef TWIS_CONFIG_DEBUG_COLOR
#define TWIS_CONFIG_DEBUG_COLOR 0
#endif

// </e>

// <e> TWI_CONFIG_LOG_ENABLED - Enables logging in the module.
//==========================================================
#ifndef TWI_CONFIG_LOG_ENABLED
#define TWI_CONFIG_LOG_ENABLED 0
#endif
// <o> TWI_CONFIG_LOG_LEVEL  - Default Severity level
 
// <0=> Off 
// <1=> Error 
// <2=> Warning 
// <3=> Info 
// <4=> Debug 

#ifndef TWI_CONFIG_LOG_LEVEL
#define TWI_CONFIG_LOG_LEVEL 3
#endif

// <o> TWI_CONFIG_INFO_COLOR  - ANSI escape code prefix.
 
// <0=> Default 
// <1=> Black 
// <2=> Red 
// <3=> Green 
// <4=> Yellow 
// <5=> Blue 
// <6=> Magenta 
// <7=> Cyan 
// <8=> White 

#ifndef TWI_CONFIG_INFO_COLOR
#define TWI_CONFIG_INFO_COLOR 0
#endif

// <o> TWI_CONFIG_DEBUG_COLOR  - ANSI escape code prefix.
 
// <0=> Default 
// <1=> Black 
// <2=> Red 
// <3=> Green 
// <4=> Yellow 
// <5=> Blue 
// <6=> Magenta 
// <7=> Cyan 
// <8=> White 

#ifndef TWI_CONFIG_DEBUG_COLOR
#define TWI_CONFIG_DEBUG_COLOR 0
#endif

// </e>

// <e> UART_CONFIG_LOG_ENABLED - Enables logging in the module.
//==========================================================
#ifndef UART_CONFIG_LOG_ENABLED
#define UART_CONFIG_LOG_ENABLED 0
#endif
// <o> UART_CONFIG_LOG_LEVEL  - Default Severity level
 
// <0=> Off 
// <1=> Error 
// <2=> Warning 
// <3=> Info 
// <4=> Debug 

#ifndef UART_CONFIG_LOG_LEVEL
#define UART_CONFIG_LOG_LEVEL 3
#endif

// <o> UART_CONFIG_INFO_COLOR  - ANSI escape code prefix.
 
// <0=> Default 
// <1=> Black 
// <2=> Red 
// <3=> Green 
// <4=> Yellow 
// <5=> Blue 
// <6=> Magenta 
// <7=> Cyan 
// <8=> White 

#ifndef UART_CONFIG_INFO_COLOR
#define UART_CONFIG_INFO_COLOR 0
#endif

// <o> UART_CONFIG_DEBUG_COLOR  - ANSI escape code prefix.
 
// <0=> Default 
// <1=> Black 
// <2=> Red 
// <3=> Green 
// <4=> Yellow 
// <5=> Blue 
// <6=> Magenta 
// <7=> Cyan 
// <8=> White 

#ifndef UART_CONFIG_DEBUG_COLOR
#define UART_CONFIG_DEBUG_COLOR 0
#endif

// </e>

// <e> USBD_CONFIG_LOG_ENABLED - Enable logging in the module
//==========================================================
#ifndef USBD_CONFIG_LOG_ENABLED
#define USBD_CONFIG_LOG_ENABLED 0
#endif
// <o> USBD_CONFIG_LOG_LEVEL  - Default Severity level
 
// <0=> Off 
// <1=> Error 
// <2=> Warning 
// <3=> Info 
// <4=> Debug 

#ifndef USBD_CONFIG_LOG_LEVEL
#define USBD_CONFIG_LOG_LEVEL 3
#endif

// <o> USBD_CONFIG_INFO_COLOR  - ANSI escape code prefix.
 
// <0=> Default 
// <1=> Black 
// <2=> Red 
// <3=> Green 
// <4=> Yellow 
// <5=> Blue 
// <6=> Magenta 
// <7=> Cyan 
// <8=> White 

#ifndef USBD_CONFIG_INFO_COLOR
#define USBD_CONFIG_INFO_COLOR 0
#endif

// <o> USBD_CONFIG_DEBUG_COLOR  - ANSI escape code prefix.
 
// <0=> Default 
// <1=> Black 
// <2=> Red 
// <3=> Green 
// <4=> Yellow 
// <5=> Blue 
// <6=> Magenta 
// <7=> Cyan 
// <8=> White 

#ifndef USBD_CONFIG_DEBUG_COLOR
#define USBD_CONFIG_DEBUG_COLOR 0
#endif

// </e>

// <e> WDT_CONFIG_LOG_ENABLED - Enables logging in the module.
//==========================================================
#ifndef WDT_CONFIG_LOG_ENABLED
#define WDT_CONFIG_LOG_ENABLED 0
#endif
// <o> WDT_CONFIG_LOG_LEVEL  - Default Severity level
 
// <0=> Off 
// <1=> Error 
// <2=> Warning 
// <3=> Info 
// <4=> Debug 

#ifndef WDT_CONFIG_LOG_LEVEL
#define WDT_CONFIG_LOG_LEVEL 3
#endif

// <o> WDT_CONFIG_INFO_COLOR  - ANSI escape code prefix.
 
// <0=> Default 
// <1=> Black 
// <2=> Red 
// <3=> Green 
// <4=> Yellow 
// <5=> Blue 
// <6=> Magenta 
// <7=> Cyan 
// <8=> White 

#ifndef WDT_CONFIG_INFO_COLOR
#define WDT_CONFIG_INFO_COLOR 0
#endif

// <o> WDT_CONFIG_DEBUG_COLOR  - ANSI escape code prefix.
 
// <0=> Default 
// <1=> Black 
// <2=> Red 
// <3=> Green 
// <4=> Yellow 
// <5=> Blue 
// <6=> Magenta 
// <7=> Cyan 
// <8=> White 

#ifndef WDT_CONFIG_DEBUG_COLOR
#define WDT_CONFIG_DEBUG_COLOR 0
#endif

// </e>

// </h> 
//==========================================================

// <h> nrf_log in nRF_Libraries 

//==========================================================
// <e> APP_TIMER_CONFIG_LOG_ENABLED - Enables logging in the module.
//==========================================================
#ifndef APP_TIMER_CONFIG_LOG_ENABLED
#define APP_TIMER_CONFIG_LOG_ENABLED 0
#endif
// <o> APP_TIMER_CONFIG_LOG_LEVEL  - Default Severity level
 
// <0=> Off 
// <1=> Error 
// <2=> Warning 
// <3=> Info 
// <4=> Debug 

#ifndef APP_TIMER_CONFIG_LOG_LEVEL
#define APP_TIMER_CONFIG_LOG_LEVEL 3
#endif

// <o> APP_TIMER_CONFIG_INITIAL_LOG_LEVEL  - Initial severity level if dynamic filtering is enabled.
 

// <i> If module generates a lot of logs, initial log level can
// <i> be decreased to prevent flooding. Severity level can be
// <i> increased on instance basis.
// <0=> Off 
// <1=> Error 
// <2=> Warning 
// <3=> Info 
// <4=> Debug 

#ifndef APP_TIMER_CONFIG_INITIAL_LOG_LEVEL
#define APP_TIMER_CONFIG_INITIAL_LOG_LEVEL 3
#endif

// <o> APP_TIMER_CONFIG_INFO_COLOR  - ANSI escape code prefix.
 
// <0=> Default 
// <1=> Black 
// <2=> Red 
// <3=> Green 
// <4=> Yellow 
// <5=> Blue 
// <6=> Magenta 
// <7=> Cyan 
// <8=> White 

#ifndef APP_TIMER_CONFIG_INFO_COLOR
#define APP_TIMER_CONFIG_INFO_COLOR 0
#endif

// <o> APP_TIMER_CONFIG_DEBUG_COLOR  - ANSI escape code prefix.
 
// <0=> Default 
// <1=> Black 
// <2=> Red 
// <3=> Green 
// <4=> Yellow 
// <5=> Blue 
// <6=> Magenta 
// <7=> Cyan 
// <8=> White 

#ifndef APP_TIMER_CONFIG_DEBUG_COLOR
#define APP_TIMER_CONFIG_DEBUG_COLOR 0
#endif

// </e>

// <e> APP_USBD_CDC_ACM_CONFIG_LOG_ENABLED - Enables logging in the module.
//==========================================================
#ifndef APP_USBD_CDC_ACM_CONFIG_LOG_ENABLED
#define APP_USBD_CDC_ACM_CONFIG_LOG_ENABLED 0
#endif
// <o> APP_USBD_CDC_ACM_CONFIG_LOG_LEVEL  - Default Severity level
 
// <0=> Off 
// <1=> Error 
// <2=> Warning 
// <3=> Info 
// <4=> Debug 

#ifndef APP_USBD_CDC_ACM_CONFIG_LOG_LEVEL
#define APP_USBD_CDC_ACM_CONFIG_LOG_LEVEL 3
#endif

// <o> APP_USBD_CDC_ACM_CONFIG_INFO_COLOR  - ANSI escape code prefix.
 
// <0=> Default 
// <1=> Black 
// <2=> Red 
// <3=> Green 
// <4=> Yellow 
// <5=> Blue 
// <6=> Magenta 
// <7=> Cyan 
// <8=> White 

#ifndef APP_USBD_CDC_ACM_CONFIG_INFO_COLOR
#define APP_USBD_CDC_ACM_CONFIG_INFO_COLOR 0
#endif

// <o> APP_USBD_CDC_ACM_CONFIG_DEBUG_COLOR  - ANSI escape code prefix.
 
// <0=> Default 
// <1=> Black 
// <2=> Red 
// <3=> Green 
// <4=> Yellow 
// <5=> Blue 
// <6=> Magenta 
// <7=> Cyan 
// <8=> White 

#ifndef APP_USBD_CDC_ACM_CONFIG_DEBUG_COLOR
#define APP_USBD_CDC_ACM_CONFIG_DEBUG_COLOR 0
#endif

// </e>

// <e> APP_USBD_DUMMY_CONFIG_LOG_ENABLED - Enables logging in the module.
//==========================================================
#ifndef APP_USBD_DUMMY_CONFIG_LOG_ENABLED
#define APP_USBD_DUMMY_CONFIG_LOG_ENABLED 0
#endif
// <o> APP_USBD_DUMMY_CONFIG_LOG_LEVEL  - Default Severity level
 
// <0=> Off 
// <1=> Error 
// <2=> Warning 
// <3=> Info 
// <4=> Debug 

#ifndef APP_USBD_DUMMY_CONFIG_LOG_LEVEL
#define APP_USBD_DUMMY_CONFIG_LOG_LEVEL 3
#endif

// <o> APP_USBD_DUMMY_CONFIG_INFO_COLOR  - ANSI escape code prefix.
 
// <0=> Default 
// <1=> Black 
// <2=> Red 
// <3=> Green 
// <4=> Yellow 
// <5=> Blue 
// <6=> Magenta 
// <7=> Cyan 
// <8=> White 

#ifndef APP_USBD_DUMMY_CONFIG_INFO_COLOR
#define APP_USBD_DUMMY_CONFIG_INFO_COLOR 0
#endif

// <o> APP_USBD_DUMMY_CONFIG_DEBUG_COLOR  - ANSI escape code prefix.
 
// <0=> Default 
// <1=> Black 
// <2=> Red 
// <3=> Green 
// <4=> Yellow 
// <5=> Blue 
// <6=> Magenta 
// <7=> Cyan 
// <8=> White 

#ifndef APP_USBD_DUMMY_CONFIG_DEBUG_COLOR
#define APP_USBD_DUMMY_CONFIG_DEBUG_COLOR 0
#endif

// </e>

// <e> APP_USBD_MSC_CONFIG_LOG_ENABLED - Enables logging in the module.
//==========================================================
#ifndef APP_USBD_MSC_CONFIG_LOG_ENABLED
#define APP_USBD_MSC_CONFIG_LOG_ENABLED 0
#endif
// <o> APP_USBD_MSC_CONFIG_LOG_LEVEL  - Default Severity level
 
// <0=> Off 
// <1=> Error 
// <2=> Warning 
// <3=> Info 
// <4=> Debug 

#ifndef APP_USBD_MSC_CONFIG_LOG_LEVEL
#define APP_USBD_MSC_CONFIG_LOG_LEVEL 3
#endif

// <o> APP_USBD_MSC_CONFIG_INFO_COLOR  - ANSI escape code prefix.
 
// <0=> Default 
// <1=> Black 
// <2=> Red 
// <3=> Green 
// <4=> Yellow 
// <5=> Blue 
// <6=> Magenta 
// <7=> Cyan 
// <8=> White 

#ifndef APP_USBD_MSC_CONFIG_INFO_COLOR
#define APP_USBD_MSC_CONFIG_INFO_COLOR 0
#endif

// <o> APP_USBD_MSC_CONFIG_DEBUG_COLOR  - ANSI escape code prefix.
 
// <0=> Default 
// <1=> Black 
// <2=> Red 
// <3=> Green 
// <4=> Yellow 
// <5=> Blue 
// <6=> Magenta 
// <7=> Cyan 
// <8=> White 

#ifndef APP_USBD_MSC_CONFIG_DEBUG_COLOR
#define APP_USBD_MSC_CONFIG_DEBUG_COLOR 0
#endif

// </e>

// <e> APP_USBD_NRF_DFU_TRIGGER_CONFIG_LOG_ENABLED - Enables logging in the module.
//==========================================================
#ifndef APP_USBD_NRF_DFU_TRIGGER_CONFIG_LOG_ENABLED
#define APP_USBD_NRF_DFU_TRIGGER_CONFIG_LOG_ENABLED 0
#endif
// <o> APP_USBD_NRF_DFU_TRIGGER_CONFIG_LOG_LEVEL  - Default Severity level
 
// <0=> Off 
// <1=> Error 
// <2=> Warning 
// <3=> Info 
// <4=> Debug 

#ifndef APP_USBD_NRF_DFU_TRIGGER_CONFIG_LOG_LEVEL
#define APP_USBD_NRF_DFU_TRIGGER_CONFIG_LOG_LEVEL 3
#endif

// <o> APP_USBD_NRF_DFU_TRIGGER_CONFIG_INFO_COLOR  - ANSI escape code prefix.
 
// <0=> Default 
// <1=> Black 
// <2=> Red 
// <3=> Green 
// <4=> Yellow 
// <5=> Blue 
// <6=> Magenta 
// <7=> Cyan 
// <8=> White 

#ifndef APP_USBD_NRF_DFU_TRIGGER_CONFIG_INFO_COLOR
#define APP_USBD_NRF_DFU_TRIGGER_CONFIG_INFO_COLOR 0
#endif

// <o> APP_USBD_NRF_DFU_TRIGGER_CONFIG_DEBUG_COLOR  - ANSI escape code prefix.
 
// <0=> Default 
// <1=> Black 
// <2=> Red 
// <3=> Green 
// <4=> Yellow 
// <5=> Blue 
// <6=> Magenta 
// <7=> Cyan 
// <8=> White 

#ifndef APP_USBD_NRF_DFU_TRIGGER_CONFIG_DEBUG_COLOR
#define APP_USBD_NRF_DFU_TRIGGER_CONFIG_DEBUG_COLOR 0
#endif

// </e>

// <e> NRF_ATFIFO_CONFIG_LOG_ENABLED - Enables logging in the module.
//==========================================================
#ifndef NRF_ATFIFO_CONFIG_LOG_ENABLED
#define NRF_ATFIFO_CONFIG_LOG_ENABLED 0
#endif
// <o> NRF_ATFIFO_CONFIG_LOG_LEVEL  - Default Severity level
 
// <0=> Off 
// <1=> Error 
// <2=> Warning 
// <3=> Info 
// <4=> Debug 

#ifndef NRF_ATFIFO_CONFIG_LOG_LEVEL
#define NRF_ATFIFO_CONFIG_LOG_LEVEL 3
#endif

// <o> NRF_ATFIFO_CONFIG_LOG_INIT_FILTER_LEVEL  - Initial severity level if dynamic filtering is enabled
 
// <0=> Off 
// <1=> Error 
// <2=> Warning 
// <3=> Info 
// <4=> Debug 

#ifndef NRF_ATFIFO_CONFIG_LOG_INIT_FILTER_LEVEL
#define NRF_ATFIFO_CONFIG_LOG_INIT_FILTER_LEVEL 3
#endif

// <o> NRF_ATFIFO_CONFIG_INFO_COLOR  - ANSI escape code prefix.
 
// <0=> Default 
// <1=> Black 
// <2=> Red 
// <3=> Green 
// <4=> Yellow 
// <5=> Blue 
// <6=> Magenta 
// <7=> Cyan 
// <8=> White 

#ifndef NRF_ATFIFO_CONFIG_INFO_COLOR
#define NRF_ATFIFO_CONFIG_INFO_COLOR 0
#endif

// <o> NRF_ATFIFO_CONFIG_DEBUG_COLOR  - ANSI escape code prefix.
 
// <0=> Default 
// <1=> Black 
// <2=> Red 
// <3=> Green 
// <4=> Yellow 
// <5=> Blue 
// <6=> Magenta 
// <7=> Cyan 
// <8=> White 

#ifndef NRF_ATFIFO_CONFIG_DEBUG_COLOR
#define NRF_ATFIFO_CONFIG_DEBUG_COLOR 0
#endif

// </e>

// <e> NRF_BALLOC_CONFIG_LOG_ENABLED - Enables logging in the module.
//==========================================================
#ifndef NRF_BALLOC_CONFIG_LOG_ENABLED
#define NRF_BALLOC_CONFIG_LOG_ENABLED 0
#endif
// <o> NRF_BALLOC_CONFIG_LOG_LEVEL  - Default Severity level
 
// <0=> Off 
// <1=> Error 
// <2=> Warning 
// <3=> Info 
// <4=> Debug 

#ifndef NRF_BALLOC_CONFIG_LOG_LEVEL
#define NRF_BALLOC_CONFIG_LOG_LEVEL 3
#endif

// <o> NRF_BALLOC_CONFIG_INITIAL_LOG_LEVEL  - Initial severity level if dynamic filtering is enabled.
 

// <i> If module generates a lot of logs, initial log level can
// <i> be decreased to prevent flooding. Severity level can be
// <i> increased on instance basis.
// <0=> Off 
// <1=> Error 
// <2=> Warning 
// <3=> Info 
// <4=> Debug 

#ifndef NRF_BALLOC_CONFIG_INITIAL_LOG_LEVEL
#define NRF_BALLOC_CONFIG_INITIAL_LOG_LEVEL 3
#endif

// <o> NRF_BALLOC_CONFIG_INFO_COLOR  - ANSI escape code prefix.
 
// <0=> Default 
// <1=> Black 
// <2=> Red 
// <3=> Green 
// <4=> Yellow 
// <5=> Blue 
// <6=> Magenta 
// <7=> Cyan 
// <8=> White 

#ifndef NRF_BALLOC_CONFIG_INFO_COLOR
#define NRF_BALLOC_CONFIG_INFO_COLOR 0
#endif

// <o> NRF_BALLOC_CONFIG_DEBUG_COLOR  - ANSI escape code prefix.
 
// <0=> Default 
// <1=> Black 
// <2=> Red 
// <3=> Green 
// <4=> Yellow 
// <5=> Blue 
// <6=> Magenta 
// <7=> Cyan 
// <8=> White 

#ifndef NRF_BALLOC_CONFIG_DEBUG_COLOR
#define NRF_BALLOC_CONFIG_DEBUG_COLOR 0
#endif

// </e>

// <e> NRF_CLI_BLE_UART_CONFIG_LOG_ENABLED - Enables logging in the module.
//==========================================================
#ifndef NRF_CLI_BLE_UART_CONFIG_LOG_ENABLED
#define NRF_CLI_BLE_UART_CONFIG_LOG_ENABLED 0
#endif
// <o> NRF_CLI_BLE_UART_CONFIG_LOG_LEVEL  - Default Severity level
 
// <0=> Off 
// <1=> Error 
// <2=> Warning 
// <3=> Info 
// <4=> Debug 

#ifndef NRF_CLI_BLE_UART_CONFIG_LOG_LEVEL
#define NRF_CLI_BLE_UART_CONFIG_LOG_LEVEL 3
#endif

// <o> NRF_CLI_BLE_UART_CONFIG_INFO_COLOR  - ANSI escape code prefix.
 
// <0=> Default 
// <1=> Black 
// <2=> Red 
// <3=> Green 
// <4=> Yellow 
// <5=> Blue 
// <6=> Magenta 
// <7=> Cyan 
// <8=> White 

#ifndef NRF_CLI_BLE_UART_CONFIG_INFO_COLOR
#define NRF_CLI_BLE_UART_CONFIG_INFO_COLOR 0
#endif

// <o> NRF_CLI_BLE_UART_CONFIG_DEBUG_COLOR  - ANSI escape code prefix.
 
// <0=> Default 
// <1=> Black 
// <2=> Red 
// <3=> Green 
// <4=> Yellow 
// <5=> Blue 
// <6=> Magenta 
// <7=> Cyan 
// <8=> White 

#ifndef NRF_CLI_BLE_UART_CONFIG_DEBUG_COLOR
#define NRF_CLI_BLE_UART_CONFIG_DEBUG_COLOR 0
#endif

// </e>

// <e> NRF_CLI_LIBUARTE_CONFIG_LOG_ENABLED - Enables logging in the module.
//==========================================================
#ifndef NRF_CLI_LIBUARTE_CONFIG_LOG_ENABLED
#define NRF_CLI_LIBUARTE_CONFIG_LOG_ENABLED 0
#endif
// <o> NRF_CLI_LIBUARTE_CONFIG_LOG_LEVEL  - Default Severity level
 
// <0=> Off 
// <1=> Error 
// <2=> Warning 
// <3=> Info 
// <4=> Debug 

#ifndef NRF_CLI_LIBUARTE_CONFIG_LOG_LEVEL
#define NRF_CLI_LIBUARTE_CONFIG_LOG_LEVEL 3
#endif

// <o> NRF_CLI_LIBUARTE_CONFIG_INFO_COLOR  - ANSI escape code prefix.
 
// <0=> Default 
// <1=> Black 
// <2=> Red 
// <3=> Green 
// <4=> Yellow 
// <5=> Blue 
// <6=> Magenta 
// <7=> Cyan 
// <8=> White 

#ifndef NRF_CLI_LIBUARTE_CONFIG_INFO_COLOR
#define NRF_CLI_LIBUARTE_CONFIG_INFO_COLOR 0
#endif

// <o> NRF_CLI_LIBUARTE_CONFIG_DEBUG_COLOR  - ANSI escape code prefix.
 
// <0=> Default 
// <1=> Black 
// <2=> Red 
// <3=> Green 
// <4=> Yellow 
// <5=> Blue 
// <6=> Magenta 
// <7=> Cyan 
// <8=> White 

#ifndef NRF_CLI_LIBUARTE_CONFIG_DEBUG_COLOR
#define NRF_CLI_LIBUARTE_CONFIG_DEBUG_COLOR 0
#endif

// </e>

// <e> NRF_CLI_UART_CONFIG_LOG_ENABLED - Enables logging in the module.
//==========================================================
#ifndef NRF_CLI_UART_CONFIG_LOG_ENABLED
#define NRF_CLI_UART_CONFIG_LOG_ENABLED 0
#endif
// <o> NRF_CLI_UART_CONFIG_LOG_LEVEL  - Default Severity level
 
// <0=> Off 
// <1=> Error 
// <2=> Warning 
// <3=> Info 
// <4=> Debug 

#ifndef NRF_CLI_UART_CONFIG_LOG_LEVEL
#define NRF_CLI_UART_CONFIG_LOG_LEVEL 3
#endif

// <o> NRF_CLI_UART_CONFIG_INFO_COLOR  - ANSI escape code prefix.
 
// <0=> Default 
// <1=> Black 
// <2=> Red 
// <3=> Green 
// <4=> Yellow 
// <5=> Blue 
// <6=> Magenta 
// <7=> Cyan 
// <8=> White 

#ifndef NRF_CLI_UART_CONFIG_INFO_COLOR
#define NRF_CLI_UART_CONFIG_INFO_COLOR 0
#endif

// <o> NRF_CLI_UART_CONFIG_DEBUG_COLOR  - ANSI escape code prefix.
 
// <0=> Default 
// <1=> Black 
// <2=> Red 
// <3=> Green 
// <4=> Yellow 
// <5=> Blue 
// <6=> Magenta 
// <7=> Cyan 
// <8=> White 

#ifndef NRF_CLI_UART_CONFIG_DEBUG_COLOR
#define NRF_CLI_UART_CONFIG_DEBUG_COLOR 0
#endif

// </e>

// <e> NRF_LIBUARTE_CONFIG_LOG_ENABLED - Enables logging in the module.
//==========================================================
#ifndef NRF_LIBUARTE_CONFIG_LOG_ENABLED
#define NRF_LIBUARTE_CONFIG_LOG_ENABLED 0
#endif
// <o> NRF_LIBUARTE_CONFIG_LOG_LEVEL  - Default Severity level
 
// <0=> Off 
// <1=> Error 
// <2=> Warning 
// <3=> Info 
// <4=> Debug 

#ifndef NRF_LIBUARTE_CONFIG_LOG_LEVEL
#define NRF_LIBUARTE_CONFIG_LOG_LEVEL 3
#endif

// <o> NRF_LIBUARTE_CONFIG_INFO_COLOR  - ANSI escape code prefix.
 
// <0=> Default 
// <1=> Black 
// <2=> Red 
// <3=> Green 
// <4=> Yellow 
// <5=> Blue 
// <6=> Magenta 
// <7=> Cyan 
// <8=> White 

#ifndef NRF_LIBUARTE_CONFIG_INFO_COLOR
#define NRF_LIBUARTE_CONFIG_INFO_COLOR 0
#endif

// <o> NRF_LIBUARTE_CONFIG_DEBUG_COLOR  - ANSI escape code prefix.
 
// <0=> Default 
// <1=> Black 
// <2=> Red 
// <3=> Green 
// <4=> Yellow 
// <5=> Blue 
// <6=> Magenta 
// <7=> Cyan 
// <8=> White 

#ifndef NRF_LIBUARTE_CONFIG_DEBUG_COLOR
#define NRF_LIBUARTE_CONFIG_DEBUG_COLOR 0
#endif

// </e>

// <e> NRF_MEMOBJ_CONFIG_LOG_ENABLED - Enables logging in the module.
//==========================================================
#ifndef NRF_MEMOBJ_CONFIG_LOG_ENABLED
#define NRF_MEMOBJ_CONFIG_LOG_ENABLED 0
#endif
// <o> NRF_MEMOBJ_CONFIG_LOG_LEVEL  - Default Severity level
 
// <0=> Off 
// <1=> Error 
// <2=> Warning 
// <3=> Info 
// <4=> Debug 

#ifndef NRF_MEMOBJ_CONFIG_LOG_LEVEL
#define NRF_MEMOBJ_CONFIG_LOG_LEVEL 3
#endif

// <o> NRF_MEMOBJ_CONFIG_INFO_COLOR  - ANSI escape code prefix.
 
// <0=> Default 
// <1=> Black 
// <2=> Red 
// <3=> Green 
// <4=> Yellow 
// <5=> Blue 
// <6=> Magenta 
// <7=> Cyan 
// <8=> White 

#ifndef NRF_MEMOBJ_CONFIG_INFO_COLOR
#define NRF_MEMOBJ_CONFIG_INFO_COLOR 0
#endif

// <o> NRF_MEMOBJ_CONFIG_DEBUG_COLOR  - ANSI escape code prefix.
 
// <0=> Default 
// <1=> Black 
// <2=> Red 
// <3=> Green 
// <4=> Yellow 
// <5=> Blue 
// <6=> Magenta 
// <7=> Cyan 
// <8=> White 

#ifndef NRF_MEMOBJ_CONFIG_DEBUG_COLOR
#define NRF_MEMOBJ_CONFIG_DEBUG_COLOR 0
#endif

// </e>

// <e> NRF_PWR_MGMT_CONFIG_LOG_ENABLED - Enables logging in the module.
//==========================================================
#ifndef NRF_PWR_MGMT_CONFIG_LOG_ENABLED
#define NRF_PWR_MGMT_CONFIG_LOG_ENABLED 0
#endif
// <o> NRF_PWR_MGMT_CONFIG_LOG_LEVEL  - Default Severity level
 
// <0=> Off 
// <1=> Error 
// <2=> Warning 
// <3=> Info 
// <4=> Debug 

#ifndef NRF_PWR_MGMT_CONFIG_LOG_LEVEL
#define NRF_PWR_MGMT_CONFIG_LOG_LEVEL 3
#endif

// <o> NRF_PWR_MGMT_CONFIG_INFO_COLOR  - ANSI escape code prefix.
 
// <0=> Default 
// <1=> Black 
// <2=> Red 
// <3=> Green 
// <4=> Yellow 
// <5=> Blue 
// <6=> Magenta 
// <7=> Cyan 
// <8=> White 

#ifndef NRF_PWR_MGMT_CONFIG_INFO_COLOR
#define NRF_PWR_MGMT_CONFIG_INFO_COLOR 0
#endif

// <o> NRF_PWR_MGMT_CONFIG_DEBUG_COLOR  - ANSI escape code prefix.
 
// <0=> Default 
// <1=> Black 
// <2=> Red 
// <3=> Green 
// <4=> Yellow 
// <5=> Blue 
// <6=> Magenta 
// <7=> Cyan 
// <8=> White 

#ifndef NRF_PWR_MGMT_CONFIG_DEBUG_COLOR
#define NRF_PWR_MGMT_CONFIG_DEBUG_COLOR 0
#endif

// </e>

// <e> NRF_QUEUE_CONFIG_LOG_ENABLED - Enables logging in the module.
//==========================================================
#ifndef NRF_QUEUE_CONFIG_LOG_ENABLED
#define NRF_QUEUE_CONFIG_LOG_ENABLED 0
#endif
// <o> NRF_QUEUE_CONFIG_LOG_LEVEL  - Default Severity level
 
// <0=> Off 
// <1=> Error 
// <2=> Warning 
// <3=> Info 
// <4=> Debug 

#ifndef NRF_QUEUE_CONFIG_LOG_LEVEL
#define NRF_QUEUE_CONFIG_LOG_LEVEL 3
#endif

// <o> NRF_QUEUE_CONFIG_LOG_INIT_FILTER_LEVEL  - Initial severity level if dynamic filtering is enabled
 
// <0=> Off 
// <1=> Error 
// <2=> Warning 
// <3=> Info 
// <4=> Debug 

#ifndef NRF_QUEUE_CONFIG_LOG_INIT_FILTER_LEVEL
#define NRF_QUEUE_CONFIG_LOG_INIT_FILTER_LEVEL 3
#endif

// <o> NRF_QUEUE_CONFIG_INFO_COLOR  - ANSI escape code prefix.
 
// <0=> Default 
// <1=> Black 
// <2=> Red 
// <3=> Green 
// <4=> Yellow 
// <5=> Blue 
// <6=> Magenta 
// <7=> Cyan 
// <8=> White 

#ifndef NRF_QUEUE_CONFIG_INFO_COLOR
#define NRF_QUEUE_CONFIG_INFO_COLOR 0
#endif

// <o> NRF_QUEUE_CONFIG_DEBUG_COLOR  - ANSI escape code prefix.
 
// <0=> Default 
// <1=> Black 
// <2=> Red 
// <3=> Green 
// <4=> Yellow 
// <5=> Blue 
// <6=> Magenta 
// <7=> Cyan 
// <8=> White 

#ifndef NRF_QUEUE_CONFIG_DEBUG_COLOR
#define NRF_QUEUE_CONFIG_DEBUG_COLOR 0
#endif

// </e>

// <e> NRF_SDH_ANT_LOG_ENABLED - Enable logging in SoftDevice handler (ANT) module.
//==========================================================
#ifndef NRF_SDH_ANT_LOG_ENABLED
#define NRF_SDH_ANT_LOG_ENABLED 0
#endif
// <o> NRF_SDH_ANT_LOG_LEVEL  - Default Severity level
 
// <0=> Off 
// <1=> Error 
// <2=> Warning 
// <3=> Info 
// <4=> Debug 

#ifndef NRF_SDH_ANT_LOG_LEVEL
#define NRF_SDH_ANT_LOG_LEVEL 3
#endif

// <o> NRF_SDH_ANT_INFO_COLOR  - ANSI escape code prefix.
 
// <0=> Default 
// <1=> Black 
// <2=> Red 
// <3=> Green 
// <4=> Yellow 
// <5=> Blue 
// <6=> Magenta 
// <7=> Cyan 
// <8=> White 

#ifndef NRF_SDH_ANT_INFO_COLOR
#define NRF_SDH_ANT_INFO_COLOR 0
#endif

// <o> NRF_SDH_ANT_DEBUG_COLOR  - ANSI escape code prefix.
 
// <0=> Default 
// <1=> Black 
// <2=> Red 
// <3=> Green 
// <4=> Yellow 
// <5=> Blue 
// <6=> Magenta 
// <7=> Cyan 
// <8=> White 

#ifndef NRF_SDH_ANT_DEBUG_COLOR
#define NRF_SDH_ANT_DEBUG_COLOR 0
#endif

// </e>

// <e> NRF_SDH_BLE_LOG_ENABLED - Enable logging in SoftDevice handler (BLE) module.
//==========================================================
#ifndef NRF_SDH_BLE_LOG_ENABLED
#define NRF_SDH_BLE_LOG_ENABLED 1
#endif
// <o> NRF_SDH_BLE_LOG_LEVEL  - Default Severity level
 
// <0=> Off 
// <1=> Error 
// <2=> Warning 
// <3=> Info 
// <4=> Debug 

#ifndef NRF_SDH_BLE_LOG_LEVEL
#define NRF_SDH_BLE_LOG_LEVEL 3
#endif

// <o> NRF_SDH_BLE_INFO_COLOR  - ANSI escape code prefix.
 
// <0=> Default 
// <1=> Black 
// <2=> Red 
// <3=> Green 
// <4=> Yellow 
// <5=> Blue 
// <6=> Magenta 
// <7=> Cyan 
// <8=> White 

#ifndef NRF_SDH_BLE_INFO_COLOR
#define NRF_SDH_BLE_INFO_COLOR 0
#endif

// <o> NRF_SDH_BLE_DEBUG_COLOR  - ANSI escape code prefix.
 
// <0=> Default 
// <1=> Black 
// <2=> Red 
// <3=> Green 
// <4=> Yellow 
// <5=> Blue 
// <6=> Magenta 
// <7=> Cyan 
// <8=> White 

#ifndef NRF_SDH_BLE_DEBUG_COLOR
#define NRF_SDH_BLE_DEBUG_COLOR 0
#endif

// </e>

// <e> NRF_SDH_LOG_ENABLED - Enable logging in SoftDevice handler module.
//==========================================================
#ifndef NRF_SDH_LOG_ENABLED
#define NRF_SDH_LOG_ENABLED 1
#endif
// <o> NRF_SDH_LOG_LEVEL  - Default Severity level
 
// <0=> Off 
// <1=> Error 
// <2=> Warning 
// <3=> Info 
// <4=> Debug 

#ifndef NRF_SDH_LOG_LEVEL
#define NRF_SDH_LOG_LEVEL 3
#endif

// <o> NRF_SDH_INFO_COLOR  - ANSI escape code prefix.
 
// <0=> Default 
// <1=> Black 
// <2=> Red 
// <3=> Green 
// <4=> Yellow 
// <5=> Blue 
// <6=> Magenta 
// <7=> Cyan 
// <8=> White 

#ifndef NRF_SDH_INFO_COLOR
#define NRF_SDH_INFO_COLOR 0
#endif

// <o> NRF_SDH_DEBUG_COLOR  - ANSI escape code prefix.
 
// <0=> Default 
// <1=> Black 
// <2=> Red 
// <3=> Green 
// <4=> Yellow 
// <5=> Blue 
// <6=> Magenta 
// <7=> Cyan 
// <8=> White 

#ifndef NRF_SDH_DEBUG_COLOR
#define NRF_SDH_DEBUG_COLOR 0
#endif

// </e>

// <e> NRF_SDH_SOC_LOG_ENABLED - Enable logging in SoftDevice handler (SoC) module.
//==========================================================
#ifndef NRF_SDH_SOC_LOG_ENABLED
#define NRF_SDH_SOC_LOG_ENABLED 1
#endif
// <o> NRF_SDH_SOC_LOG_LEVEL  - Default Severity level
 
// <0=> Off 
// <1=> Error 
// <2=> Warning 
// <3=> Info 
// <4=> Debug 

#ifndef NRF_SDH_SOC_LOG_LEVEL
#define NRF_SDH_SOC_LOG_LEVEL 3
#endif

// <o> NRF_SDH_SOC_INFO_COLOR  - ANSI escape code prefix.
 
// <0=> Default 
// <1=> Black 
// <2=> Red 
// <3=> Green 
// <4=> Yellow 
// <5=> Blue 
// <6=> Magenta 
// <7=> Cyan 
// <8=> White 

#ifndef NRF_SDH_SOC_INFO_COLOR
#define NRF_SDH_SOC_INFO_COLOR 0
#endif

// <o> NRF_SDH_SOC_DEBUG_COLOR  - ANSI escape code prefix.
 
// <0=> Default 
// <1=> Black 
// <2=> Red 
// <3=> Green 
// <4=> Yellow 
// <5=> Blue 
// <6=> Magenta 
// <7=> Cyan 
// <8=> White 

#ifndef NRF_SDH_SOC_DEBUG_COLOR
#define NRF_SDH_SOC_DEBUG_COLOR 0
#endif

// </e>

// <e> NRF_SORTLIST_CONFIG_LOG_ENABLED - Enables logging in the module.
//==========================================================
#ifndef NRF_SORTLIST_CONFIG_LOG_ENABLED
#define NRF_SORTLIST_CONFIG_LOG_ENABLED 0
#endif
// <o> NRF_SORTLIST_CONFIG_LOG_LEVEL  - Default Severity level
 
// <0=> Off 
// <1=> Error 
// <2=> Warning 
// <3=> Info 
// <4=> Debug 

#ifndef NRF_SORTLIST_CONFIG_LOG_LEVEL
#define NRF_SORTLIST_CONFIG_LOG_LEVEL 3
#endif

// <o> NRF_SORTLIST_CONFIG_INFO_COLOR  - ANSI escape code prefix.
 
// <0=> Default 
// <1=> Black 
// <2=> Red 
// <3=> Green 
// <4=> Yellow 
// <5=> Blue 
// <6=> Magenta 
// <7=> Cyan 
// <8=> White 

#ifndef NRF_SORTLIST_CONFIG_INFO_COLOR
#define NRF_SORTLIST_CONFIG_INFO_COLOR 0
#endif

// <o> NRF_SORTLIST_CONFIG_DEBUG_COLOR  - ANSI escape code prefix.
 
// <0=> Default 
// <1=> Black 
// <2=> Red 
// <3=> Green 
// <4=> Yellow 
// <5=> Blue 
// <6=> Magenta 
// <7=> Cyan 
// <8=> White 

#ifndef NRF_SORTLIST_CONFIG_DEBUG_COLOR
#define NRF_SORTLIST_CONFIG_DEBUG_COLOR 0
#endif

// </e>

// <e> NRF_TWI_SENSOR_CONFIG_LOG_ENABLED - Enables logging in the module.
//==========================================================
#ifndef NRF_TWI_SENSOR_CONFIG_LOG_ENABLED
#define NRF_TWI_SENSOR_CONFIG_LOG_ENABLED 0
#endif
// <o> NRF_TWI_SENSOR_CONFIG_LOG_LEVEL  - Default Severity level
 
// <0=> Off 
// <1=> Error 
// <2=> Warning 
// <3=> Info 
// <4=> Debug 

#ifndef NRF_TWI_SENSOR_CONFIG_LOG_LEVEL
#define NRF_TWI_SENSOR_CONFIG_LOG_LEVEL 3
#endif

// <o> NRF_TWI_SENSOR_CONFIG_INFO_COLOR  - ANSI escape code prefix.
 
// <0=> Default 
// <1=> Black 
// <2=> Red 
// <3=> Green 
// <4=> Yellow 
// <5=> Blue 
// <6=> Magenta 
// <7=> Cyan 
// <8=> White 

#ifndef NRF_TWI_SENSOR_CONFIG_INFO_COLOR
#define NRF_TWI_SENSOR_CONFIG_INFO_COLOR 0
#endif

// <o> NRF_TWI_SENSOR_CONFIG_DEBUG_COLOR  - ANSI escape code prefix.
 
// <0=> Default 
// <1=> Black 
// <2=> Red 
// <3=> Green 
// <4=> Yellow 
// <5=> Blue 
// <6=> Magenta 
// <7=> Cyan 
// <8=> White 

#ifndef NRF_TWI_SENSOR_CONFIG_DEBUG_COLOR
#define NRF_TWI_SENSOR_CONFIG_DEBUG_COLOR 0
#endif

// </e>

// </h> 
//==========================================================

// <h> nrf_log in nRF_Serialization 

//==========================================================
// <e> SER_HAL_TRANSPORT_CONFIG_LOG_ENABLED - Enables logging in the module.
//==========================================================
#ifndef SER_HAL_TRANSPORT_CONFIG_LOG_ENABLED
#define SER_HAL_TRANSPORT_CONFIG_LOG_ENABLED 0
#endif
// <o> SER_HAL_TRANSPORT_CONFIG_LOG_LEVEL  - Default Severity level
 
// <0=> Off 
// <1=> Error 
// <2=> Warning 
// <3=> Info 
// <4=> Debug 

#ifndef SER_HAL_TRANSPORT_CONFIG_LOG_LEVEL
#define SER_HAL_TRANSPORT_CONFIG_LOG_LEVEL 3
#endif

// <o> SER_HAL_TRANSPORT_CONFIG_INFO_COLOR  - ANSI escape code prefix.
 
// <0=> Default 
// <1=> Black 
// <2=> Red 
// <3=> Green 
// <4=> Yellow 
// <5=> Blue 
// <6=> Magenta 
// <7=> Cyan 
// <8=> White 

#ifndef SER_HAL_TRANSPORT_CONFIG_INFO_COLOR
#define SER_HAL_TRANSPORT_CONFIG_INFO_COLOR 0
#endif

// <o> SER_HAL_TRANSPORT_CONFIG_DEBUG_COLOR  - ANSI escape code prefix.
 
// <0=> Default 
// <1=> Black 
// <2=> Red 
// <3=> Green 
// <4=> Yellow 
// <5=> Blue 
// <6=> Magenta 
// <7=> Cyan 
// <8=> White 

#ifndef SER_HAL_TRANSPORT_CONFIG_DEBUG_COLOR
#define SER_HAL_TRANSPORT_CONFIG_DEBUG_COLOR 0
#endif

// </e>

// </h> 
//==========================================================

// </h> 
//==========================================================

// </h> 
//==========================================================

// </h> 
//==========================================================

// <h> nRF_SoftDevice 

//==========================================================
// <e> NRF_SDH_BLE_ENABLED - nrf_sdh_ble - SoftDevice BLE event handler
//==========================================================
#ifndef NRF_SDH_BLE_ENABLED
#define NRF_SDH_BLE_ENABLED 1
#endif
// <h> BLE Stack configuration - Stack configuration parameters

// <i> The SoftDevice handler will configure the stack with these parameters when calling @ref nrf_sdh_ble_default_cfg_set.
// <i> Other libraries might depend on these values; keep them up-to-date even if you are not explicitely calling @ref nrf_sdh_ble_default_cfg_set.
//==========================================================
// <o> NRF_SDH_BLE_GAP_DATA_LENGTH   <27-251> 


// <i> Requested BLE GAP data length to be negotiated.

#ifndef NRF_SDH_BLE_GAP_DATA_LENGTH
#define NRF_SDH_BLE_GAP_DATA_LENGTH 27
#endif

// <o> NRF_SDH_BLE_PERIPHERAL_LINK_COUNT - Maximum number of peripheral links. 
#ifndef NRF_SDH_BLE_PERIPHERAL_LINK_COUNT
#define NRF_SDH_BLE_PERIPHERAL_LINK_COUNT 1
#endif

// <o> NRF_SDH_BLE_CENTRAL_LINK_COUNT - Maximum number of central links. 
#ifndef NRF_SDH_BLE_CENTRAL_LINK_COUNT
#define NRF_SDH_BLE_CENTRAL_LINK_COUNT 0
#endif

// <o> NRF_SDH_BLE_TOTAL_LINK_COUNT - Total link count. 
// <i> Maximum number of total concurrent connections using the default configuration.

#ifndef NRF_SDH_BLE_TOTAL_LINK_COUNT
#define NRF_SDH_BLE_TOTAL_LINK_COUNT 1
#endif

// <o> NRF_SDH_BLE_GAP_EVENT_LENGTH - GAP event length. 
// <i> The time set aside for this connection on every connection interval in 1.25 ms units.

#ifndef NRF_SDH_BLE_GAP_EVENT_LENGTH
#define NRF_SDH_BLE_GAP_EVENT_LENGTH 6
#endif

// <o> NRF_SDH_BLE_GATT_MAX_MTU_SIZE - Static maximum MTU size. 
#ifndef NRF_SDH_BLE_GATT_MAX_MTU_SIZE
#define NRF_SDH_BLE_GATT_MAX_MTU_SIZE 23
#endif

// <o> NRF_SDH_BLE_GATTS_ATTR_TAB_SIZE - Attribute Table size in bytes. The size must be a multiple of 4. 
#ifndef NRF_SDH_BLE_GATTS_ATTR_TAB_SIZE
#define NRF_SDH_BLE_GATTS_ATTR_TAB_SIZE 1408
#endif

// <o> NRF_SDH_BLE_VS_UUID_COUNT - The number of vendor-specific UUIDs. 
#ifndef NRF_SDH_BLE_VS_UUID_COUNT
#define NRF_SDH_BLE_VS_UUID_COUNT 1
#endif

// <q> NRF_SDH_BLE_SERVICE_CHANGED  - Include the Service Changed characteristic in the Attribute Table.
 

#ifndef NRF_SDH_BLE_SERVICE_CHANGED
#define NRF_SDH_BLE_SERVICE_CHANGED 0
#endif

// </h> 
//==========================================================

// <h> BLE Observers - Observers and priority levels

//==========================================================
// <o> NRF_SDH_BLE_OBSERVER_PRIO_LEVELS - Total number of priority levels for BLE observers. 
// <i> This setting configures the number of priority levels available for BLE event handlers.
// <i> The priority level of a handler determines the order in which it receives events, with respect to other handlers.

#ifndef NRF_SDH_BLE_OBSERVER_PRIO_LEVELS
#define NRF_SDH_BLE_OBSERVER_PRIO_LEVELS 4
#endif

// <h> BLE Observers priorities - Invididual priorities

//==========================================================
// <o> BLE_ADV_BLE_OBSERVER_PRIO  
// <i> Priority with which BLE events are dispatched to the Advertising module.

#ifndef BLE_ADV_BLE_OBSERVER_PRIO
#define BLE_ADV_BLE_OBSERVER_PRIO 1
#endif

// <o> BLE_ANCS_C_BLE_OBSERVER_PRIO  
// <i> Priority with which BLE events are dispatched to the Apple Notification Service Client.

#ifndef BLE_ANCS_C_BLE_OBSERVER_PRIO
#define BLE_ANCS_C_BLE_OBSERVER_PRIO 2
#endif

// <o> BLE_ANS_C_BLE_OBSERVER_PRIO  
// <i> Priority with which BLE events are dispatched to the Alert Notification Service Client.

#ifndef BLE_ANS_C_BLE_OBSERVER_PRIO
#define BLE_ANS_C_BLE_OBSERVER_PRIO 2
#endif

// <o> BLE_BAS_BLE_OBSERVER_PRIO  
// <i> Priority with which BLE events are dispatched to the Battery Service.

#ifndef BLE_BAS_BLE_OBSERVER_PRIO
#define BLE_BAS_BLE_OBSERVER_PRIO 2
#endif

// <o> BLE_BAS_C_BLE_OBSERVER_PRIO  
// <i> Priority with which BLE events are dispatched to the Battery Service Client.

#ifndef BLE_BAS_C_BLE_OBSERVER_PRIO
#define BLE_BAS_C_BLE_OBSERVER_PRIO 2
#endif

// <o> BLE_BPS_BLE_OBSERVER_PRIO  
// <i> Priority with which BLE events are dispatched to the Blood Pressure Service.

#ifndef BLE_BPS_BLE_OBSERVER_PRIO
#define BLE_BPS_BLE_OBSERVER_PRIO 2
#endif

// <o> BLE_CONN_PARAMS_BLE_OBSERVER_PRIO  
// <i> Priority with which BLE events are dispatched to the Connection parameters module.

#ifndef BLE_CONN_PARAMS_BLE_OBSERVER_PRIO
#define BLE_CONN_PARAMS_BLE_OBSERVER_PRIO 1
#endif

// <o> BLE_CONN_STATE_BLE_OBSERVER_PRIO  
// <i> Priority with which BLE events are dispatched to the Connection State module.

#ifndef BLE_CONN_STATE_BLE_OBSERVER_PRIO
#define BLE_CONN_STATE_BLE_OBSERVER_PRIO 0
#endif

// <o> BLE_CSCS_BLE_OBSERVER_PRIO  
// <i> Priority with which BLE events are dispatched to the Cycling Speed and Cadence Service.

#ifndef BLE_CSCS_BLE_OBSERVER_PRIO
#define BLE_CSCS_BLE_OBSERVER_PRIO 2
#endif

// <o> BLE_CTS_C_BLE_OBSERVER_PRIO  
// <i> Priority with which BLE events are dispatched to the Current Time Service Client.

#ifndef BLE_CTS_C_BLE_OBSERVER_PRIO
#define BLE_CTS_C_BLE_OBSERVER_PRIO 2
#endif

// <o> BLE_DB_DISC_BLE_OBSERVER_PRIO  
// <i> Priority with which BLE events are dispatched to the Database Discovery module.

#ifndef BLE_DB_DISC_BLE_OBSERVER_PRIO
#define BLE_DB_DISC_BLE_OBSERVER_PRIO 1
#endif

// <o> BLE_DFU_BLE_OBSERVER_PRIO  
// <i> Priority with which BLE events are dispatched to the DFU Service.

#ifndef BLE_DFU_BLE_OBSERVER_PRIO
#define BLE_DFU_BLE_OBSERVER_PRIO 2
#endif

// <o> BLE_DIS_C_BLE_OBSERVER_PRIO  
// <i> Priority with which BLE events are dispatched to the Device Information Client.

#ifndef BLE_DIS_C_BLE_OBSERVER_PRIO
#define BLE_DIS_C_BLE_OBSERVER_PRIO 2
#endif

// <o> BLE_GLS_BLE_OBSERVER_PRIO  
// <i> Priority with which BLE events are dispatched to the Glucose Service.

#ifndef BLE_GLS_BLE_OBSERVER_PRIO
#define BLE_GLS_BLE_OBSERVER_PRIO 2
#endif

// <o> BLE_HIDS_BLE_OBSERVER_PRIO  
// <i> Priority with which BLE events are dispatched to the Human Interface Device Service.

#ifndef BLE_HIDS_BLE_OBSERVER_PRIO
#define BLE_HIDS_BLE_OBSERVER_PRIO 2
#endif

// <o> BLE_HRS_BLE_OBSERVER_PRIO  
// <i> Priority with which BLE events are dispatched to the Heart Rate Service.

#ifndef BLE_HRS_BLE_OBSERVER_PRIO
#define BLE_HRS_BLE_OBSERVER_PRIO 2
#endif

// <o> BLE_HRS_C_BLE_OBSERVER_PRIO  
// <i> Priority with which BLE events are dispatched to the Heart Rate Service Client.

#ifndef BLE_HRS_C_BLE_OBSERVER_PRIO
#define BLE_HRS_C_BLE_OBSERVER_PRIO 2
#endif

// <o> BLE_HTS_BLE_OBSERVER_PRIO  
// <i> Priority with which BLE events are dispatched to the Health Thermometer Service.

#ifndef BLE_HTS_BLE_OBSERVER_PRIO
#define BLE_HTS_BLE_OBSERVER_PRIO 2
#endif

// <o> BLE_IAS_BLE_OBSERVER_PRIO  
// <i> Priority with which BLE events are dispatched to the Immediate Alert Service.

#ifndef BLE_IAS_BLE_OBSERVER_PRIO
#define BLE_IAS_BLE_OBSERVER_PRIO 2
#endif

// <o> BLE_IAS_C_BLE_OBSERVER_PRIO  
// <i> Priority with which BLE events are dispatched to the Immediate Alert Service Client.

#ifndef BLE_IAS_C_BLE_OBSERVER_PRIO
#define BLE_IAS_C_BLE_OBSERVER_PRIO 2
#endif

// <o> BLE_LBS_BLE_OBSERVER_PRIO  
// <i> Priority with which BLE events are dispatched to the LED Button Service.

#ifndef BLE_LBS_BLE_OBSERVER_PRIO
#define BLE_LBS_BLE_OBSERVER_PRIO 2
#endif

// <o> BLE_LBS_C_BLE_OBSERVER_PRIO  
// <i> Priority with which BLE events are dispatched to the LED Button Service Client.

#ifndef BLE_LBS_C_BLE_OBSERVER_PRIO
#define BLE_LBS_C_BLE_OBSERVER_PRIO 2
#endif

// <o> BLE_LESC_OBSERVER_PRIO  
// <i> Priority with which BLE events are dispatched to the BLE LESC module.

#ifndef BLE_LESC_OBSERVER_PRIO
#define BLE_LESC_OBSERVER_PRIO 2
#endif

// <o> BLE_LLS_BLE_OBSERVER_PRIO  
// <i> Priority with which BLE events are dispatched to the Link Loss Service.

#ifndef BLE_LLS_BLE_OBSERVER_PRIO
#define BLE_LLS_BLE_OBSERVER_PRIO 2
#endif

// <o> BLE_LNS_BLE_OBSERVER_PRIO  
// <i> Priority with which BLE events are dispatched to the Location Navigation Service.

#ifndef BLE_LNS_BLE_OBSERVER_PRIO
#define BLE_LNS_BLE_OBSERVER_PRIO 2
#endif

// <o> BLE_NUS_BLE_OBSERVER_PRIO  
// <i> Priority with which BLE events are dispatched to the UART Service.

#ifndef BLE_NUS_BLE_OBSERVER_PRIO
#define BLE_NUS_BLE_OBSERVER_PRIO 2
#endif

// <o> BLE_NUS_C_BLE_OBSERVER_PRIO  
// <i> Priority with which BLE events are dispatched to the UART Central Service.

#ifndef BLE_NUS_C_BLE_OBSERVER_PRIO
#define BLE_NUS_C_BLE_OBSERVER_PRIO 2
#endif

// <o> BLE_OTS_BLE_OBSERVER_PRIO  
// <i> Priority with which BLE events are dispatched to the Object transfer service.

#ifndef BLE_OTS_BLE_OBSERVER_PRIO
#define BLE_OTS_BLE_OBSERVER_PRIO 2
#endif

// <o> BLE_OTS_C_BLE_OBSERVER_PRIO  
// <i> Priority with which BLE events are dispatched to the Object transfer service client.

#ifndef BLE_OTS_C_BLE_OBSERVER_PRIO
#define BLE_OTS_C_BLE_OBSERVER_PRIO 2
#endif

// <o> BLE_RSCS_BLE_OBSERVER_PRIO  
// <i> Priority with which BLE events are dispatched to the Running Speed and Cadence Service.

#ifndef BLE_RSCS_BLE_OBSERVER_PRIO
#define BLE_RSCS_BLE_OBSERVER_PRIO 2
#endif

// <o> BLE_RSCS_C_BLE_OBSERVER_PRIO  
// <i> Priority with which BLE events are dispatched to the Running Speed and Cadence Client.

#ifndef BLE_RSCS_C_BLE_OBSERVER_PRIO
#define BLE_RSCS_C_BLE_OBSERVER_PRIO 2
#endif

// <o> BLE_TPS_BLE_OBSERVER_PRIO  
// <i> Priority with which BLE events are dispatched to the TX Power Service.

#ifndef BLE_TPS_BLE_OBSERVER_PRIO
#define BLE_TPS_BLE_OBSERVER_PRIO 2
#endif

// <o> BSP_BTN_BLE_OBSERVER_PRIO  
// <i> Priority with which BLE events are dispatched to the Button Control module.

#ifndef BSP_BTN_BLE_OBSERVER_PRIO
#define BSP_BTN_BLE_OBSERVER_PRIO 1
#endif

// <o> NFC_BLE_PAIR_LIB_BLE_OBSERVER_PRIO  
// <i> Priority with which BLE events are dispatched to the NFC pairing library.

#ifndef NFC_BLE_PAIR_LIB_BLE_OBSERVER_PRIO
#define NFC_BLE_PAIR_LIB_BLE_OBSERVER_PRIO 1
#endif

// <o> NFC_BLE_PAIR_LIB_BLE_OBSERVER_PRIO  
// <i> Priority with which BLE events are dispatched to the NFC pairing library.

#ifndef NFC_BLE_PAIR_LIB_BLE_OBSERVER_PRIO
#define NFC_BLE_PAIR_LIB_BLE_OBSERVER_PRIO 1
#endif

// <o> NFC_BLE_PAIR_LIB_BLE_OBSERVER_PRIO  
// <i> Priority with which BLE events are dispatched to the NFC pairing library.

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
#define NFC_BLE_PAIR_LIB_BLE_OBSERVER_PRIO 1
#endif

// <o> NRF_BLE_BMS_BLE_OBSERVER_PRIO  
// <i> Priority with which BLE events are dispatched to the Bond Management Service.

#ifndef NRF_BLE_BMS_BLE_OBSERVER_PRIO
#define NRF_BLE_BMS_BLE_OBSERVER_PRIO 2
#endif

// <o> NRF_BLE_CGMS_BLE_OBSERVER_PRIO  
// <i> Priority with which BLE events are dispatched to the Contiuon Glucose Monitoring Service.

#ifndef NRF_BLE_CGMS_BLE_OBSERVER_PRIO
#define NRF_BLE_CGMS_BLE_OBSERVER_PRIO 2
#endif

// <o> NRF_BLE_ES_BLE_OBSERVER_PRIO  
// <i> Priority with which BLE events are dispatched to the Eddystone module.

#ifndef NRF_BLE_ES_BLE_OBSERVER_PRIO
#define NRF_BLE_ES_BLE_OBSERVER_PRIO 2
#endif

// <o> NRF_BLE_GATTS_C_BLE_OBSERVER_PRIO  
// <i> Priority with which BLE events are dispatched to the GATT Service Client.

#ifndef NRF_BLE_GATTS_C_BLE_OBSERVER_PRIO
#define NRF_BLE_GATTS_C_BLE_OBSERVER_PRIO 2
#endif

// <o> NRF_BLE_GATT_BLE_OBSERVER_PRIO  
// <i> Priority with which BLE events are dispatched to the GATT module.

#ifndef NRF_BLE_GATT_BLE_OBSERVER_PRIO
#define NRF_BLE_GATT_BLE_OBSERVER_PRIO 1
#endif

// <o> NRF_BLE_QWR_BLE_OBSERVER_PRIO  
// <i> Priority with which BLE events are dispatched to the Queued writes module.

#ifndef NRF_BLE_QWR_BLE_OBSERVER_PRIO
#define NRF_BLE_QWR_BLE_OBSERVER_PRIO 2
#endif

// <o> PM_BLE_OBSERVER_PRIO - Priority with which BLE events are dispatched to the Peer Manager module. 
#ifndef PM_BLE_OBSERVER_PRIO
#define PM_BLE_OBSERVER_PRIO 1
#endif

// </h> 
//==========================================================

// </h> 
//==========================================================


// </e>

// <e> NRF_SDH_ENABLED - nrf_sdh - SoftDevice handler
//==========================================================
#ifndef NRF_SDH_ENABLED
#define NRF_SDH_ENABLED 1
#endif
// <h> Dispatch model 

// <i> This setting configures how Stack events are dispatched to the application.
//==========================================================
// <o> NRF_SDH_DISPATCH_MODEL
 

// <i> NRF_SDH_DISPATCH_MODEL_INTERRUPT: SoftDevice events are passed to the application from the interrupt context.
// <i> NRF_SDH_DISPATCH_MODEL_APPSH: SoftDevice events are scheduled using @ref app_scheduler.
// <i> NRF_SDH_DISPATCH_MODEL_POLLING: SoftDevice events are to be fetched manually.
// <0=> NRF_SDH_DISPATCH_MODEL_INTERRUPT 
// <1=> NRF_SDH_DISPATCH_MODEL_APPSH 
// <2=> NRF_SDH_DISPATCH_MODEL_POLLING 

#ifndef NRF_SDH_DISPATCH_MODEL
#define NRF_SDH_DISPATCH_MODEL 0
#endif

// </h> 
//==========================================================

// <h> Clock - SoftDevice clock configuration

//==========================================================
// <o> NRF_SDH_CLOCK_LF_SRC  - SoftDevice clock source.
 
// <0=> NRF_CLOCK_LF_SRC_RC 
// <1=> NRF_CLOCK_LF_SRC_XTAL 
// <2=> NRF_CLOCK_LF_SRC_SYNTH 

#ifndef NRF_SDH_CLOCK_LF_SRC
#define NRF_SDH_CLOCK_LF_SRC 1
#endif

// <o> NRF_SDH_CLOCK_LF_RC_CTIV - SoftDevice calibration timer interval. 
#ifndef NRF_SDH_CLOCK_LF_RC_CTIV
#define NRF_SDH_CLOCK_LF_RC_CTIV 0
#endif

// <o> NRF_SDH_CLOCK_LF_RC_TEMP_CTIV - SoftDevice calibration timer interval under constant temperature. 
// <i> How often (in number of calibration intervals) the RC oscillator shall be calibrated
// <i>  if the temperature has not changed.

#ifndef NRF_SDH_CLOCK_LF_RC_TEMP_CTIV
#define NRF_SDH_CLOCK_LF_RC_TEMP_CTIV 0
#endif

// <o> NRF_SDH_CLOCK_LF_ACCURACY  - External clock accuracy used in the LL to compute timing.
 
// <0=> NRF_CLOCK_LF_ACCURACY_250_PPM 
// <1=> NRF_CLOCK_LF_ACCURACY_500_PPM 
// <2=> NRF_CLOCK_LF_ACCURACY_150_PPM 
// <3=> NRF_CLOCK_LF_ACCURACY_100_PPM 
// <4=> NRF_CLOCK_LF_ACCURACY_75_PPM 
// <5=> NRF_CLOCK_LF_ACCURACY_50_PPM 
// <6=> NRF_CLOCK_LF_ACCURACY_30_PPM 
// <7=> NRF_CLOCK_LF_ACCURACY_20_PPM 
// <8=> NRF_CLOCK_LF_ACCURACY_10_PPM 
// <9=> NRF_CLOCK_LF_ACCURACY_5_PPM 
// <10=> NRF_CLOCK_LF_ACCURACY_2_PPM 
// <11=> NRF_CLOCK_LF_ACCURACY_1_PPM 

#ifndef NRF_SDH_CLOCK_LF_ACCURACY
#define NRF_SDH_CLOCK_LF_ACCURACY 7
#endif

// </h> 
//==========================================================

// <h> SDH Observers - Observers and priority levels

//==========================================================
// <o> NRF_SDH_REQ_OBSERVER_PRIO_LEVELS - Total number of priority levels for request observers. 
// <i> This setting configures the number of priority levels available for the SoftDevice request event handlers.
// <i> The priority level of a handler determines the order in which it receives events, with respect to other handlers.

#ifndef NRF_SDH_REQ_OBSERVER_PRIO_LEVELS
#define NRF_SDH_REQ_OBSERVER_PRIO_LEVELS 2
#endif

// <o> NRF_SDH_STATE_OBSERVER_PRIO_LEVELS - Total number of priority levels for state observers. 
// <i> This setting configures the number of priority levels available for the SoftDevice state event handlers.
// <i> The priority level of a handler determines the order in which it receives events, with respect to other handlers.

#ifndef NRF_SDH_STATE_OBSERVER_PRIO_LEVELS
#define NRF_SDH_STATE_OBSERVER_PRIO_LEVELS 2
#endif
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
