IoTReady/low-power-nrf52-weighing-scale/firmware/bootloader/components/softdevice/s112/headers/ble_gatts.h

/*
 * Copyright (c) 2011 - 2017, Nordic Semiconductor ASA
 * All rights reserved.
 *
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
 * 3. Neither the name of Nordic Semiconductor ASA nor the names of its
 *    contributors may be used to endorse or promote products derived from this
 *    software without specific prior written permission.
 *
 * 4. This software, with or without modification, must only be used with a
 *    Nordic Semiconductor ASA integrated circuit.
 *
 * 5. Any software provided in binary form under this license must not be reverse
 *    engineered, decompiled, modified and/or disassembled.
 *
 * THIS SOFTWARE IS PROVIDED BY NORDIC SEMICONDUCTOR ASA "AS IS" AND ANY EXPRESS
 * OR IMPLIED WARRANTIES, INCLUDING, BUT NOT LIMITED TO, THE IMPLIED WARRANTIES
 * OF MERCHANTABILITY, NONINFRINGEMENT, AND FITNESS FOR A PARTICULAR PURPOSE ARE
 * DISCLAIMED. IN NO EVENT SHALL NORDIC SEMICONDUCTOR ASA OR CONTRIBUTORS BE
 * LIABLE FOR ANY DIRECT, INDIRECT, INCIDENTAL, SPECIAL, EXEMPLARY, OR
 * CONSEQUENTIAL DAMAGES (INCLUDING, BUT NOT LIMITED TO, PROCUREMENT OF SUBSTITUTE
 * GOODS OR SERVICES; LOSS OF USE, DATA, OR PROFITS; OR BUSINESS INTERRUPTION)
 * HOWEVER CAUSED AND ON ANY THEORY OF LIABILITY, WHETHER IN CONTRACT, STRICT
 * LIABILITY, OR TORT (INCLUDING NEGLIGENCE OR OTHERWISE) ARISING IN ANY WAY OUT
 * OF THE USE OF THIS SOFTWARE, EVEN IF ADVISED OF THE POSSIBILITY OF SUCH DAMAGE.
 */

/**
  @addtogroup BLE_GATTS Generic Attribute Profile (GATT) Server
  @{
  @brief  Definitions and prototypes for the GATTS interface.
 */

#ifndef BLE_GATTS_H__
#define BLE_GATTS_H__

#include <stdint.h>
#include "nrf_svc.h"
#include "nrf_error.h"
#include "ble_hci.h"
#include "ble_ranges.h"
#include "ble_types.h"
#include "ble_err.h"
#include "ble_gatt.h"
#include "ble_gap.h"

#ifdef __cplusplus
extern "C" {
#endif

/** @addtogroup BLE_GATTS_ENUMERATIONS Enumerations
 * @{ */

/**
 * @brief GATTS API SVC numbers.
 */
enum BLE_GATTS_SVCS
{
  SD_BLE_GATTS_SERVICE_ADD = BLE_GATTS_SVC_BASE, /**< Add a service. */
  SD_BLE_GATTS_INCLUDE_ADD,                      /**< Add an included service. */
  SD_BLE_GATTS_CHARACTERISTIC_ADD,               /**< Add a characteristic. */
  SD_BLE_GATTS_DESCRIPTOR_ADD,                   /**< Add a generic attribute. */
  SD_BLE_GATTS_VALUE_SET,                        /**< Set an attribute value. */
  SD_BLE_GATTS_VALUE_GET,                        /**< Get an attribute value. */
  SD_BLE_GATTS_HVX,                              /**< Handle Value Notification or Indication. */
  SD_BLE_GATTS_SERVICE_CHANGED,                  /**< Perform a Service Changed Indication to one or more peers. */
  SD_BLE_GATTS_RW_AUTHORIZE_REPLY,               /**< Reply to an authorization request for a read or write operation on one or more attributes. */
  SD_BLE_GATTS_SYS_ATTR_SET,                     /**< Set the persistent system attributes for a connection. */
  SD_BLE_GATTS_SYS_ATTR_GET,                     /**< Retrieve the persistent system attributes. */
  SD_BLE_GATTS_INITIAL_USER_HANDLE_GET,          /**< Retrieve the first valid user handle. */
  SD_BLE_GATTS_ATTR_GET,                         /**< Retrieve the UUID and/or metadata of an attribute. */
  SD_BLE_GATTS_EXCHANGE_MTU_REPLY                /**< Reply to Exchange MTU Request. */
};

/**
 * @brief GATT Server Event IDs.
 */
enum BLE_GATTS_EVTS
{
  BLE_GATTS_EVT_WRITE = BLE_GATTS_EVT_BASE,       /**< Write operation performed.                                           \n See @ref ble_gatts_evt_write_t.                 */
  BLE_GATTS_EVT_RW_AUTHORIZE_REQUEST,             /**< Read/Write Authorization request.                                    \n Reply with @ref sd_ble_gatts_rw_authorize_reply. \n See @ref ble_gatts_evt_rw_authorize_request_t. */
  BLE_GATTS_EVT_SYS_ATTR_MISSING,                 /**< A persistent system attribute access is pending.                     \n Respond with @ref sd_ble_gatts_sys_attr_set.     \n See @ref ble_gatts_evt_sys_attr_missing_t.     */
  BLE_GATTS_EVT_HVC,                              /**< Handle Value Confirmation.                                           \n See @ref ble_gatts_evt_hvc_t.                   */
  BLE_GATTS_EVT_SC_CONFIRM,                       /**< Service Changed Confirmation.                                        \n No additional event structure applies.          */
  BLE_GATTS_EVT_EXCHANGE_MTU_REQUEST,             /**< Exchange MTU Request.                                                \n Reply with @ref sd_ble_gatts_exchange_mtu_reply. \n See @ref ble_gatts_evt_exchange_mtu_request_t. */
  BLE_GATTS_EVT_TIMEOUT,                          /**< Peer failed to respond to an ATT request in time.                    \n See @ref ble_gatts_evt_timeout_t.               */
  BLE_GATTS_EVT_HVN_TX_COMPLETE                   /**< Handle Value Notification transmission complete.                     \n See @ref ble_gatts_evt_hvn_tx_complete_t.       */
};

/**@brief GATTS Configuration IDs.
 *
 * IDs that uniquely identify a GATTS configuration.
 */
enum BLE_GATTS_CFGS
{
  BLE_GATTS_CFG_SERVICE_CHANGED = BLE_GATTS_CFG_BASE, /**< Service changed configuration. */
  BLE_GATTS_CFG_ATTR_TAB_SIZE,                        /**< Attribute table size configuration. */
};

/** @} */
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
